crozone/iMac-G3-PC-Conversion/Docs/ek-momentum-2_rog_strix_x570-i-gaming__tehnicaldrawing.png

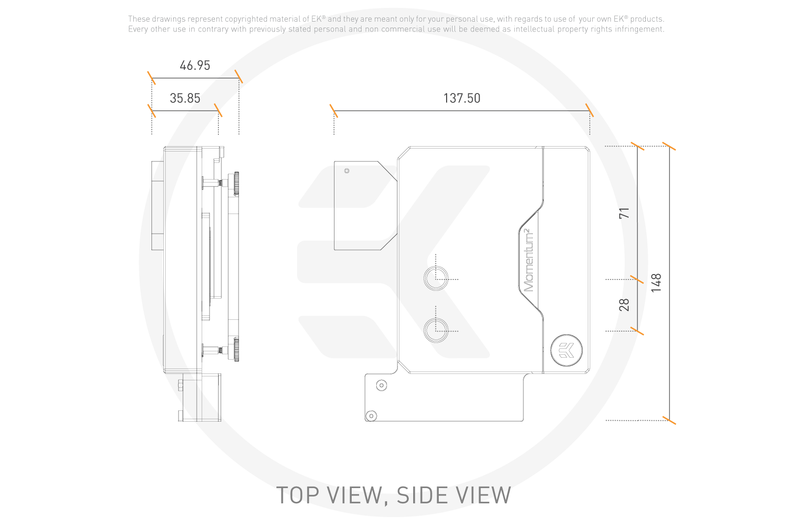
Docs/ek-momentum-2_rog_strix_x570-i-gaming__tehnicaldrawing.png
