crozone/iMac-G3-PC-Conversion/Mounting Brackets/Reservoir Mockup/Screenshots/res_0_combined.PNG

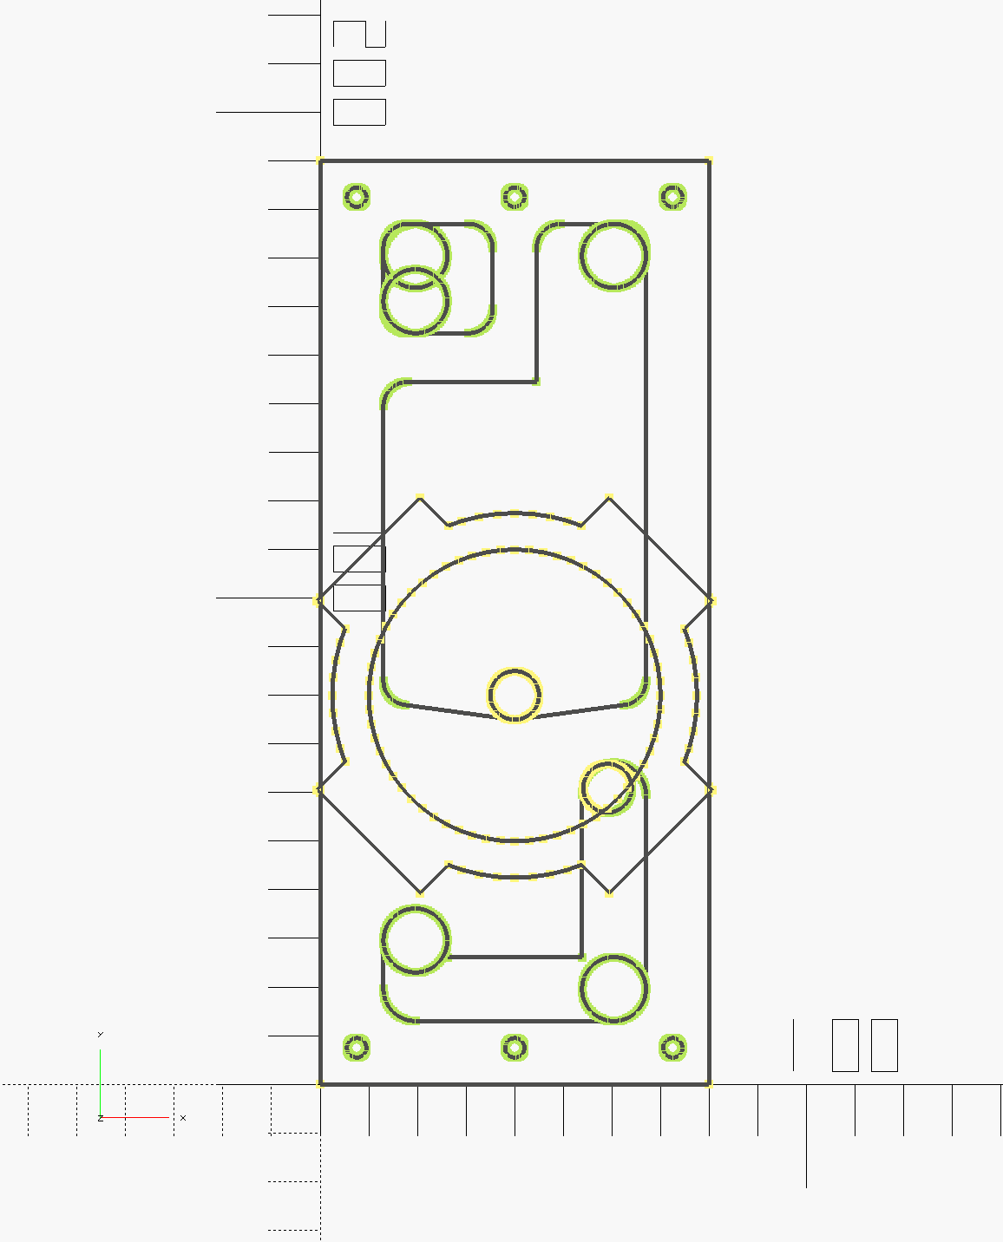
Mounting Brackets/Reservoir Mockup/Screenshots/res_0_combined.PNG
