crozone/iMac-G3-PC-Conversion/Mounting Brackets/Reservoir Mockup/Screenshots/res_2_bottom.PNG

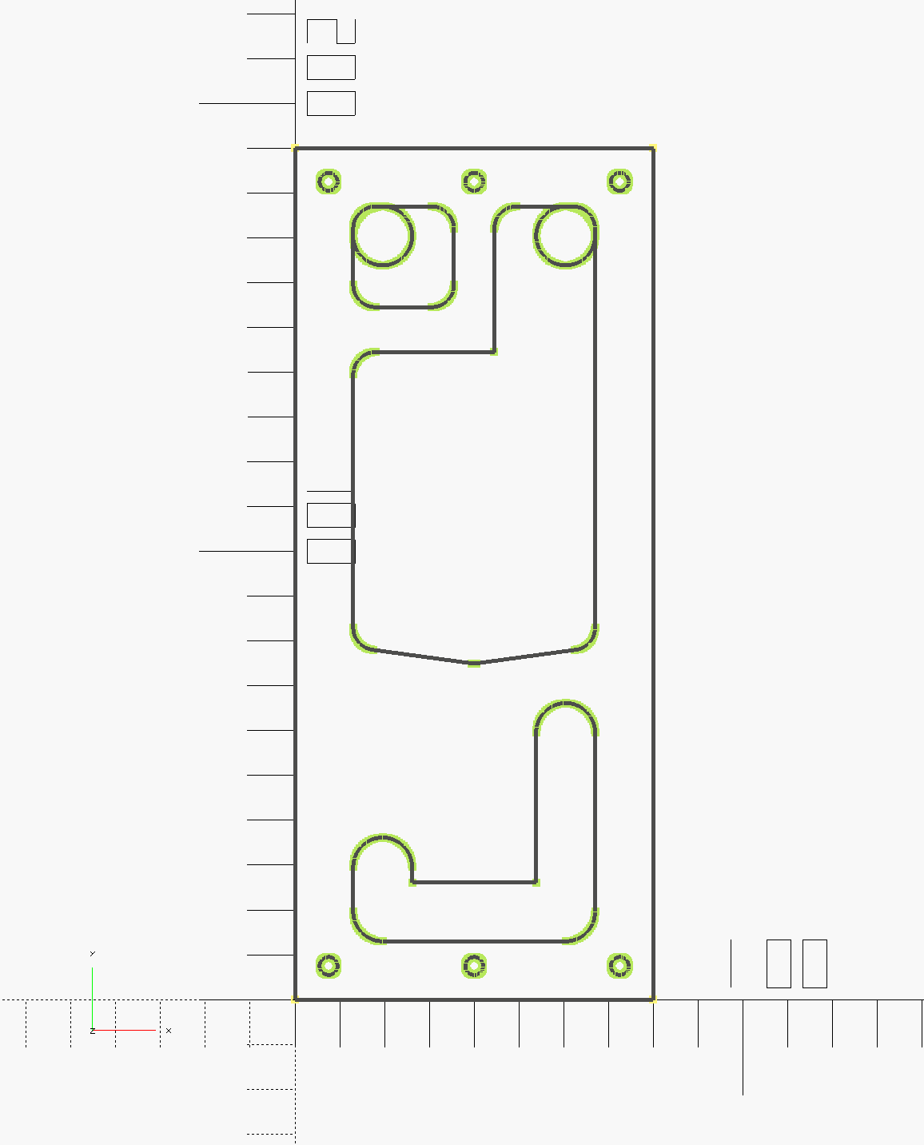
Mounting Brackets/Reservoir Mockup/Screenshots/res_2_bottom.PNG
