crozone/iMac-G3-PC-Conversion/Mounting Brackets/Reservoir Mockup/Screenshots/res_3_ortho.PNG

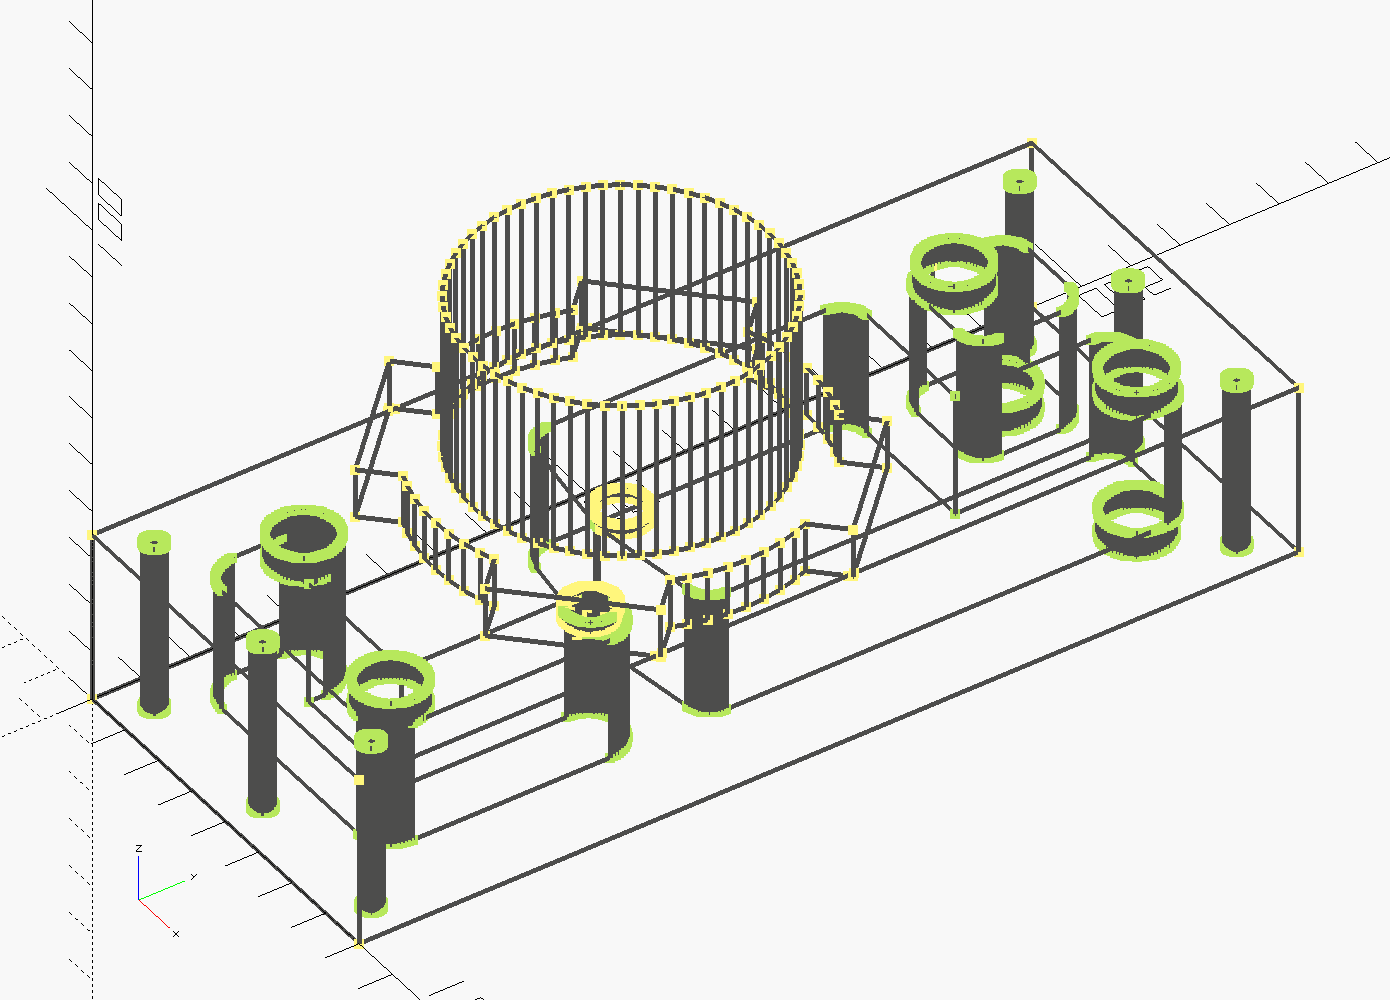
Mounting Brackets/Reservoir Mockup/Screenshots/res_3_ortho.PNG
