crozone/iMac-G3-PC-Conversion/Parts/Display Mounting/Reference Docs/LVDS Pinout.PNG

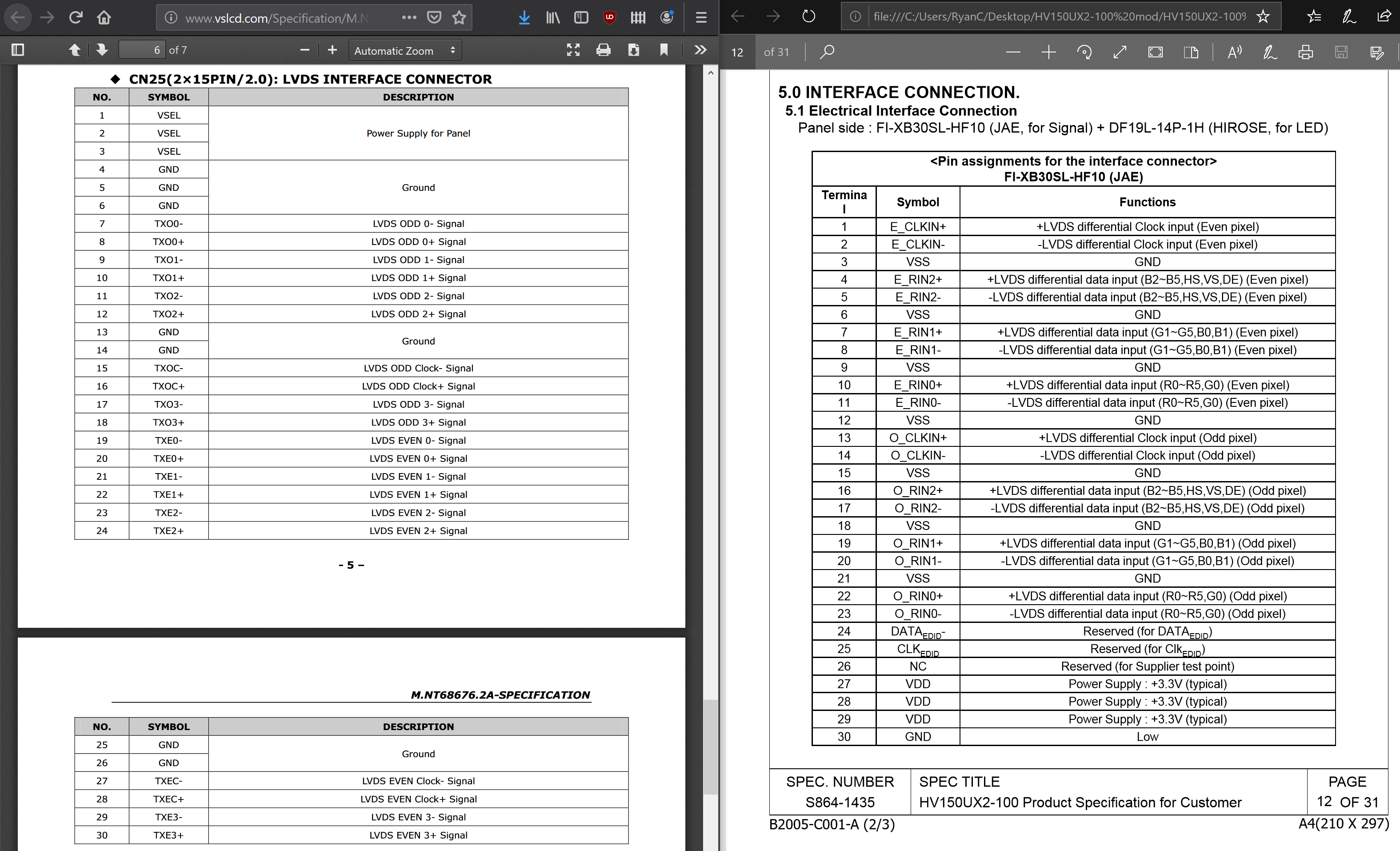
Parts/Display Mounting/Reference Docs/LVDS Pinout.PNG
