crozone/iMac-G3-PC-Conversion/Parts/Compute Sled/Docs/Bracket_drawing_1.png

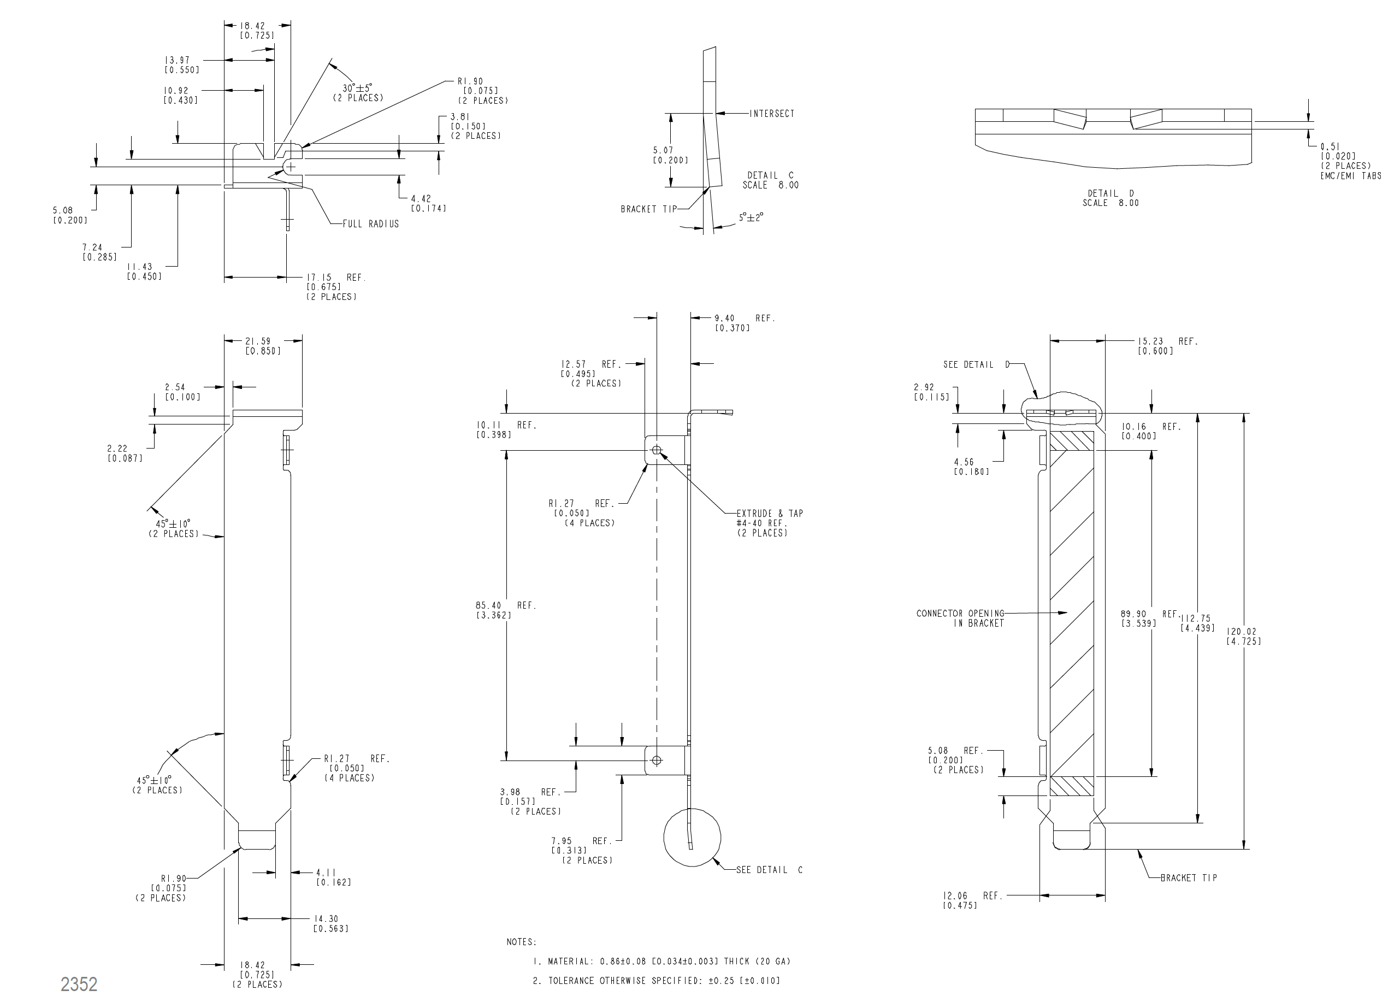
Parts/Compute Sled/Docs/Bracket_drawing_1.png
