crozone/iMac-G3-PC-Conversion/Parts/Compute Sled/Docs/Bracket_drawing_2.png

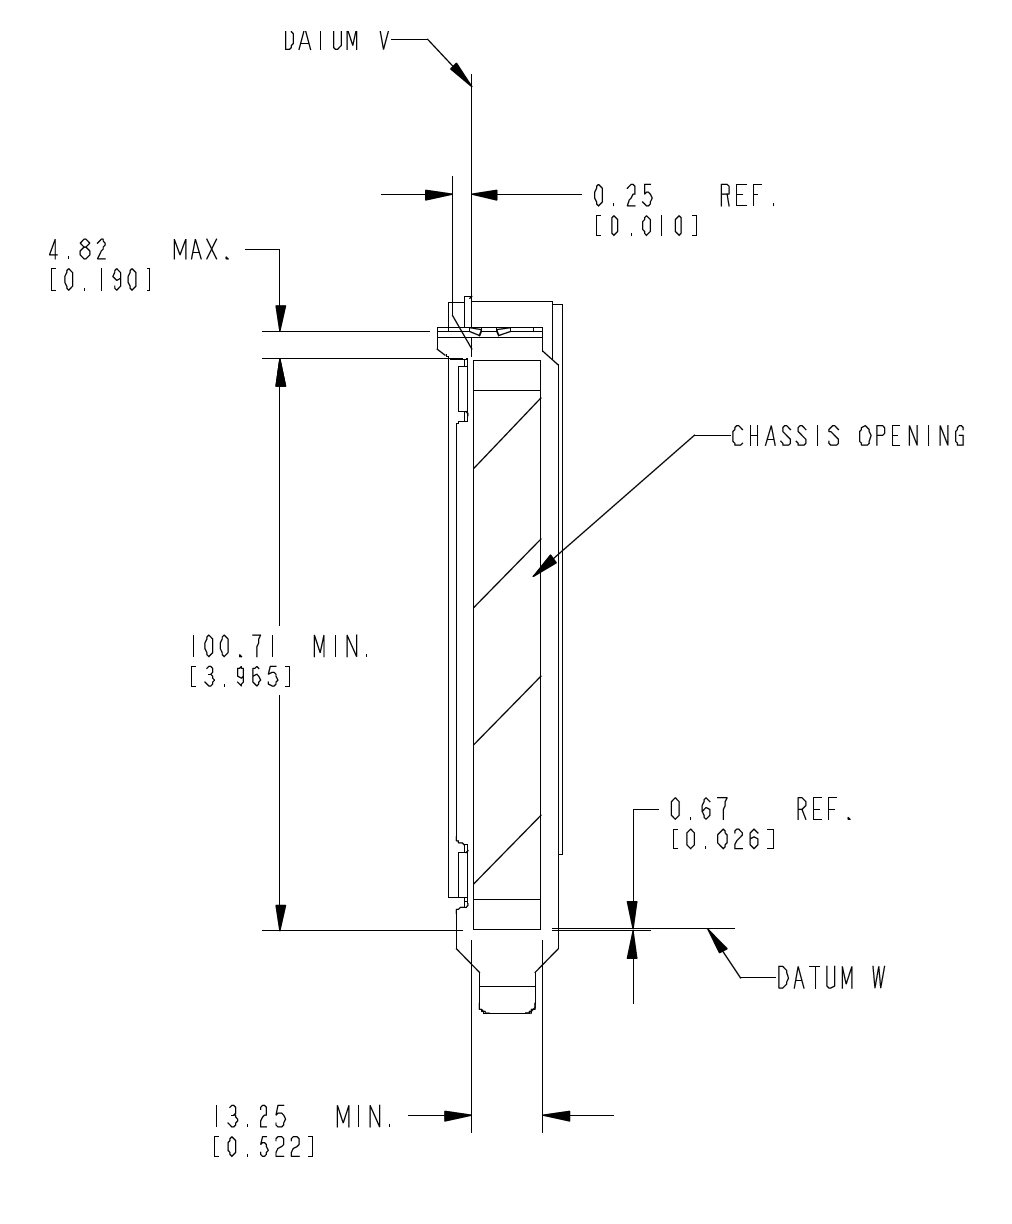
Parts/Compute Sled/Docs/Bracket_drawing_2.png
