crozone/iMac-G3-PC-Conversion/Parts/Compute Sled/Docs/hockey-stick-retention-clip.jpg

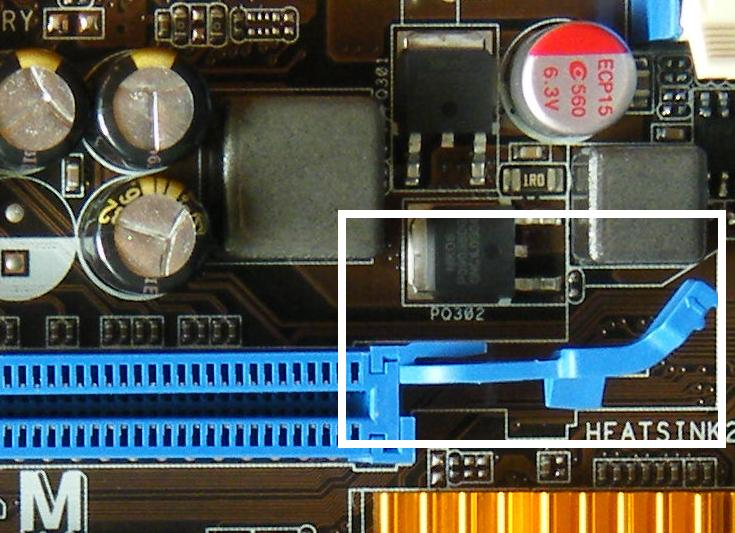
Parts/Compute Sled/Docs/hockey-stick-retention-clip.jpg
