crozone/iMac-G3-PC-Conversion/Parts/Compute Sled/Docs/mini-itx.png

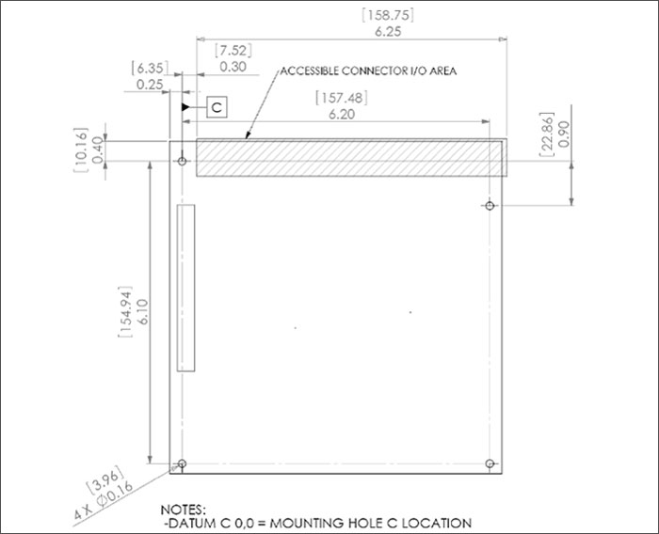
Parts/Compute Sled/Docs/mini-itx.png
