crozone/iMac-G3-PC-Conversion/Parts/Compute Sled/Docs/motherboard_drawing.png

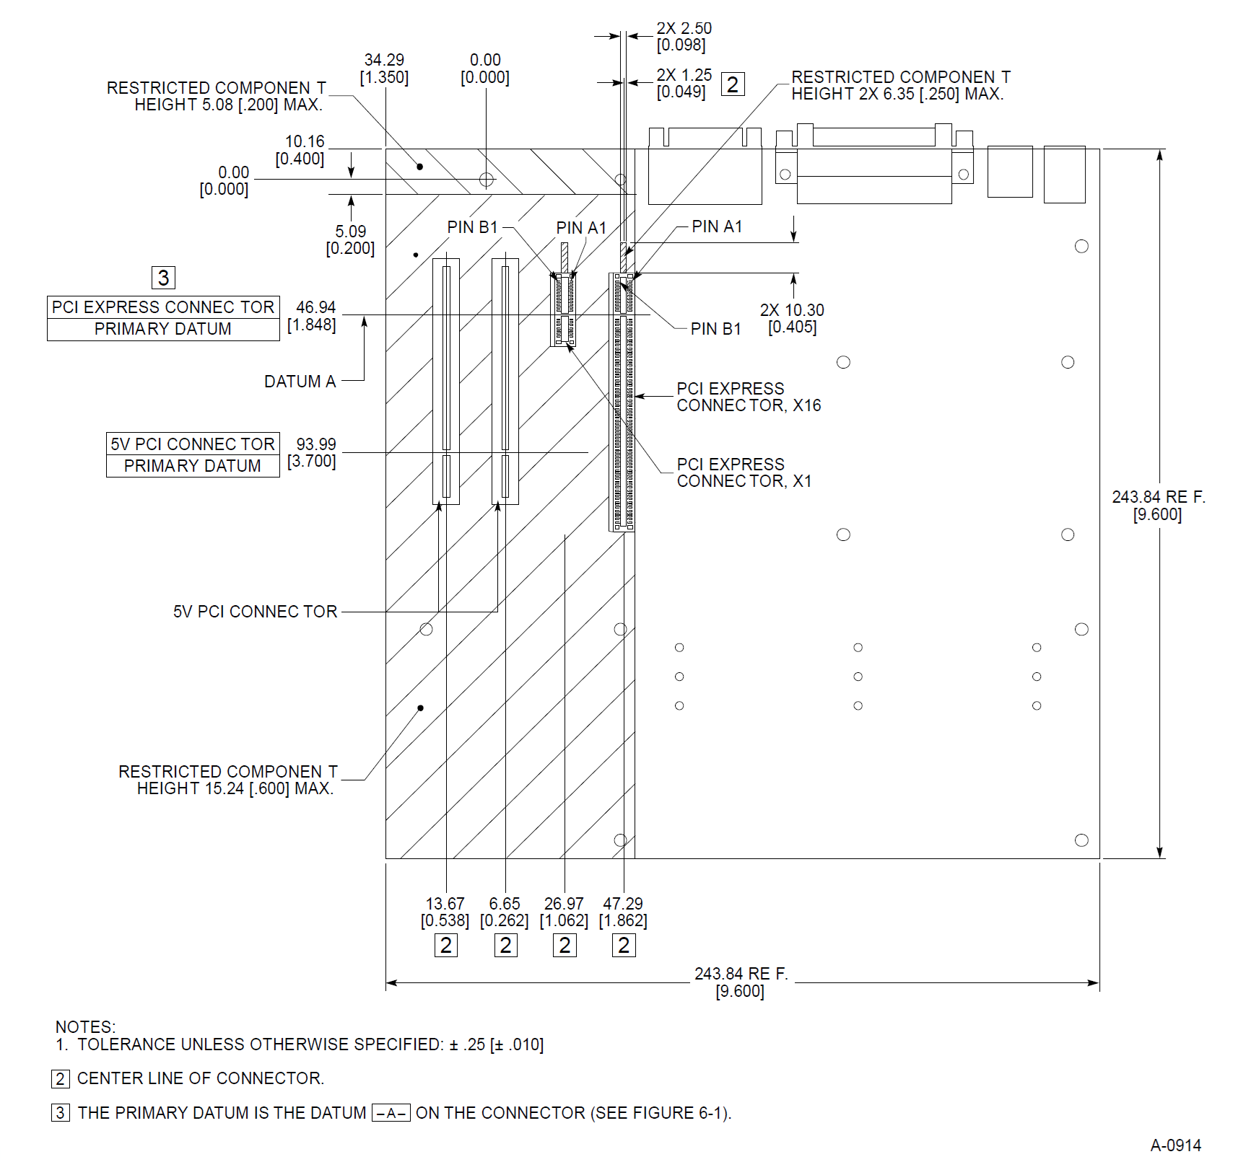
Parts/Compute Sled/Docs/motherboard_drawing.png
