crozone/iMac-G3-PC-Conversion/Parts/Compute Sled/Docs/PCIe Edge Connector Drawing.png

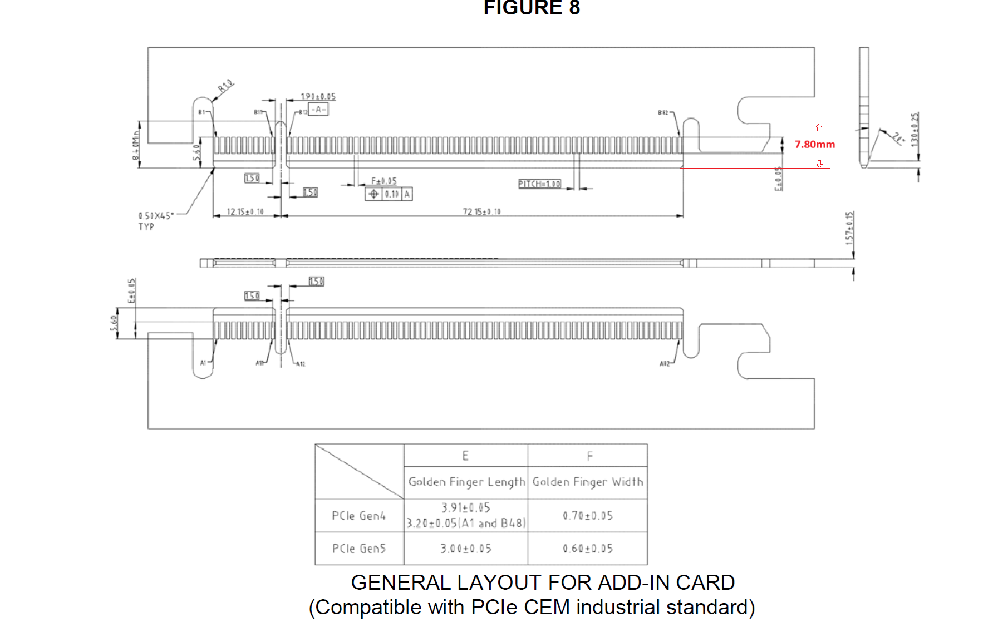
Parts/Compute Sled/Docs/PCIe Edge Connector Drawing.png
