crozone/iMac-G3-PC-Conversion/Parts/Compute Sled/Docs/PCIe_bracket_dimensions.webp

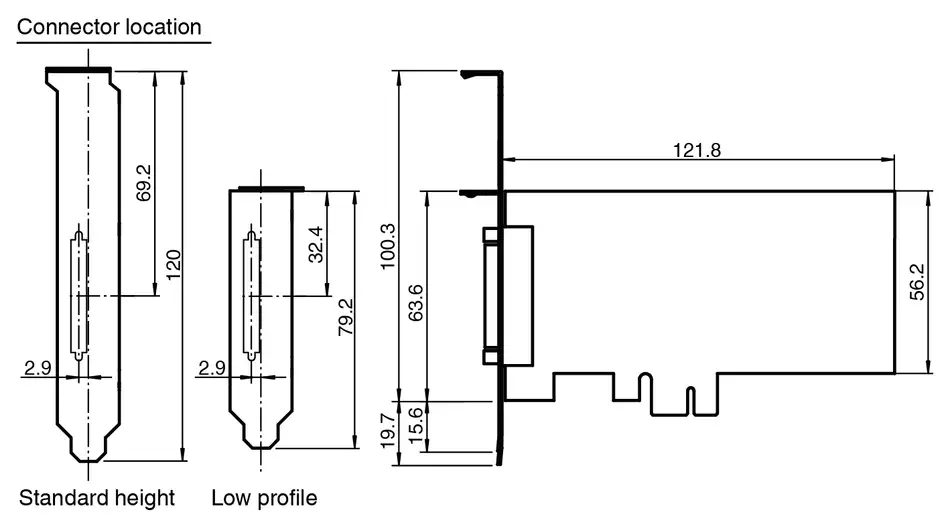
Parts/Compute Sled/Docs/PCIe_bracket_dimensions.webp
