crozone/iMac-G3-PC-Conversion/Parts/Compute Sled/Docs/PCIe_Bracket_Face_Drawing_3.jpeg

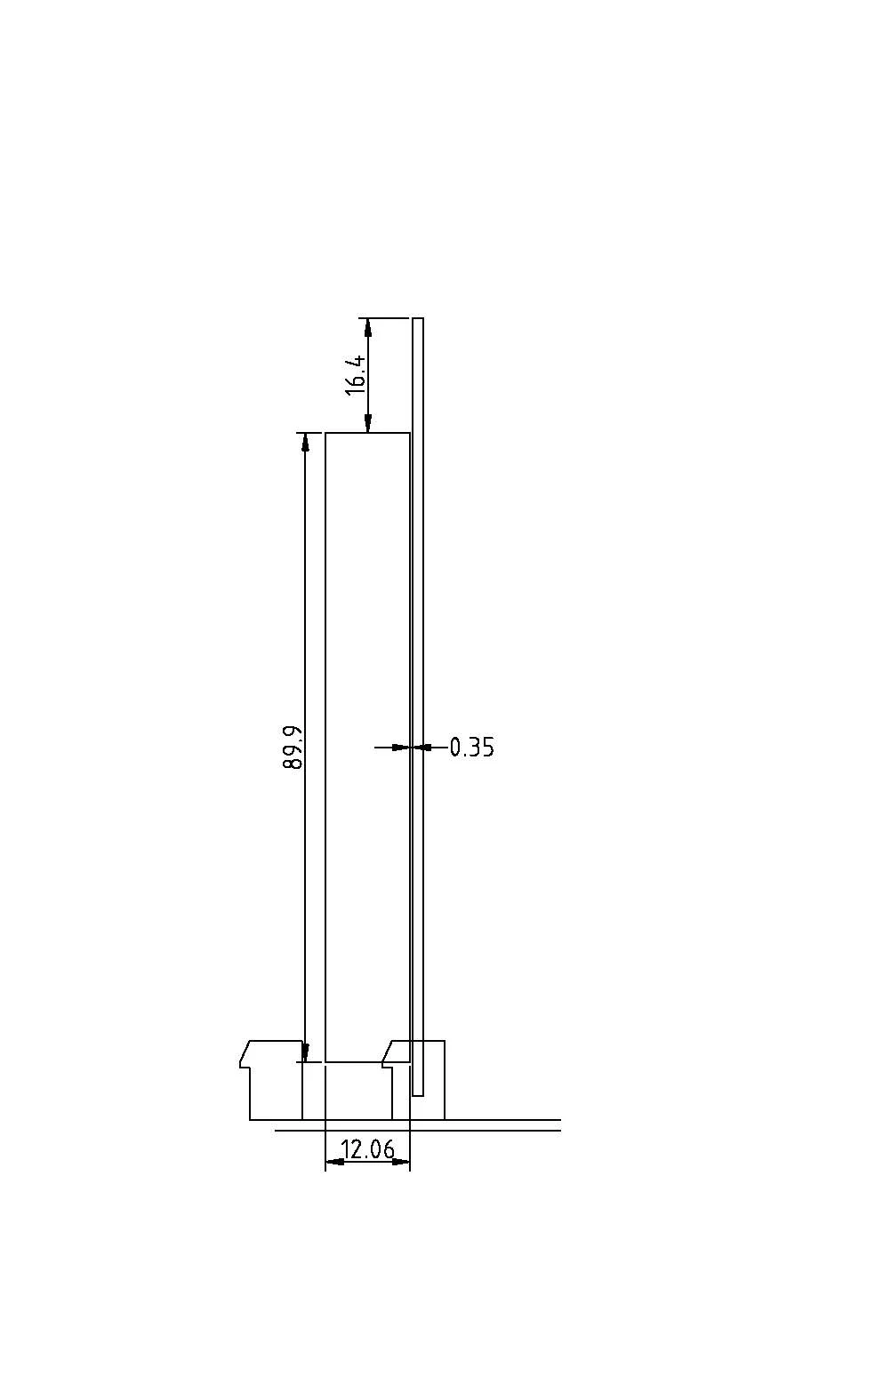
Parts/Compute Sled/Docs/PCIe_Bracket_Face_Drawing_3.jpeg
