crozone/iMac-G3-PC-Conversion/Parts/Compute Sled/Docs/PCIe_Bracket_Face_Drawing_5.jpeg

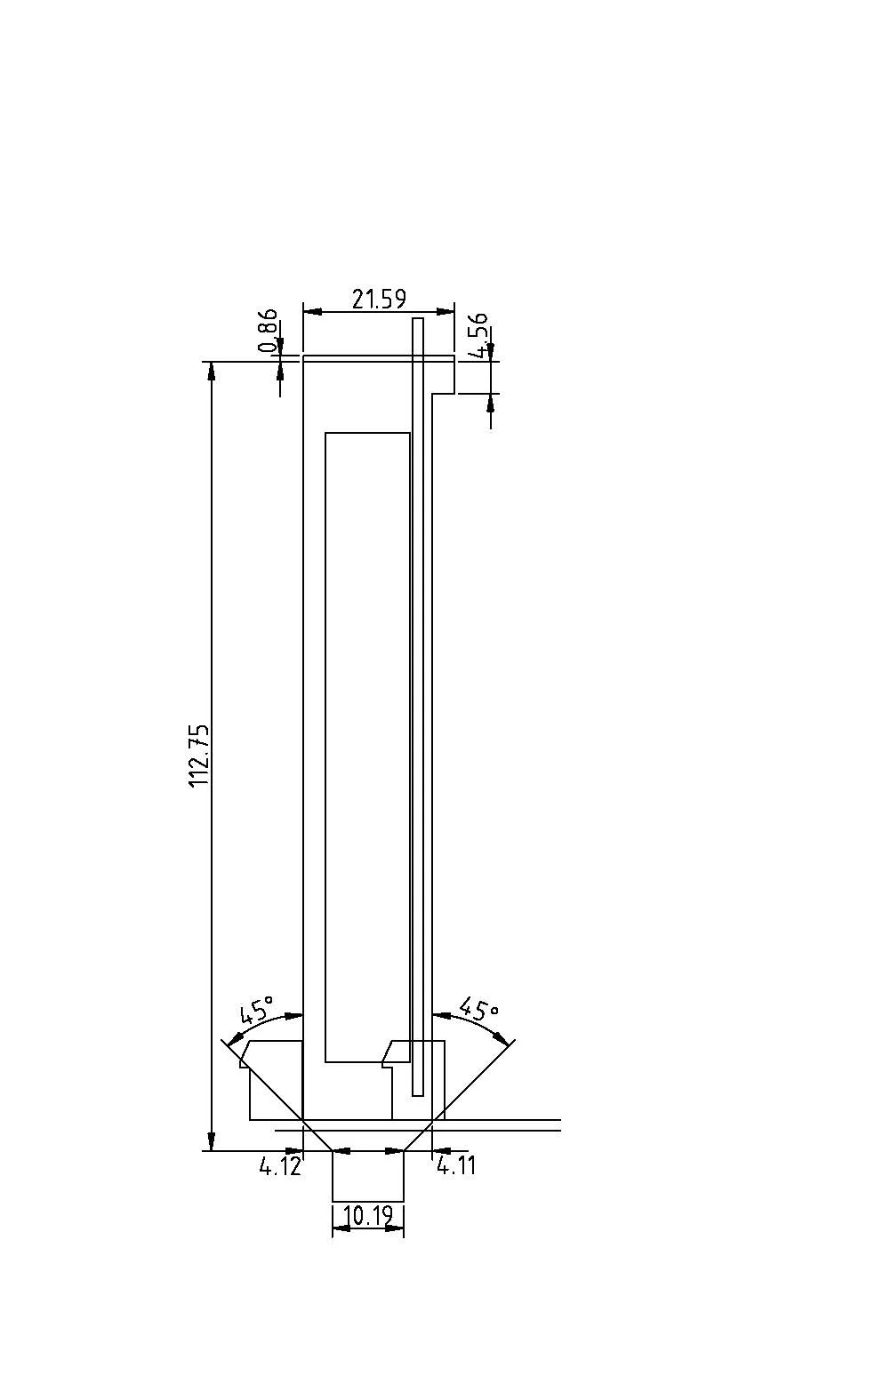
Parts/Compute Sled/Docs/PCIe_Bracket_Face_Drawing_5.jpeg
