crozone/iMac-G3-PC-Conversion/Parts/Compute Sled/Docs/PCIe_Bracket_Wing_Drawing.jpeg

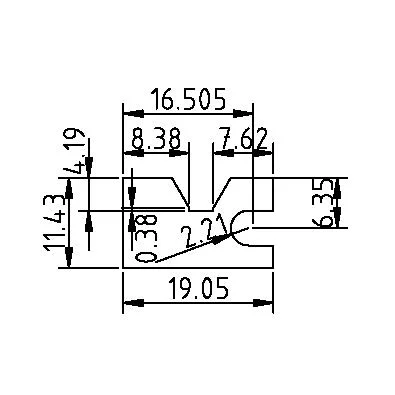
Parts/Compute Sled/Docs/PCIe_Bracket_Wing_Drawing.jpeg
