crozone/iMac-G3-PC-Conversion/Parts/Compute Sled/Docs/pcie_card_dimensions.png

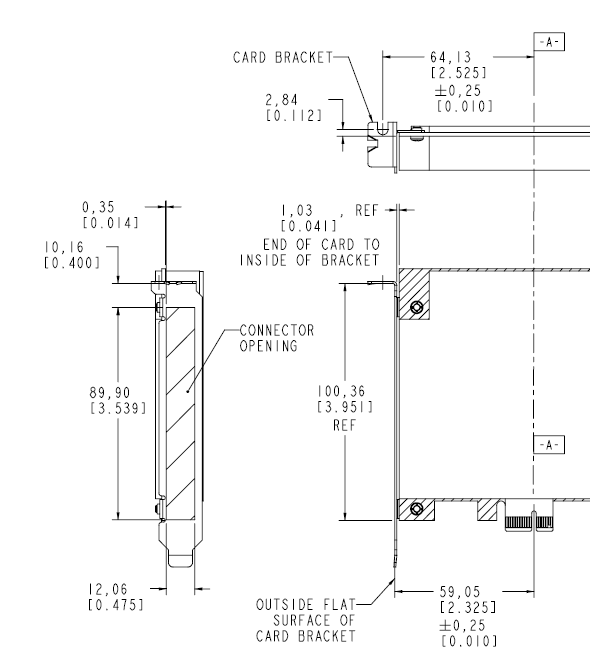
Parts/Compute Sled/Docs/pcie_card_dimensions.png
