crozone/iMac-G3-PC-Conversion/Parts/Compute Sled/Docs/PCIe_Slot_Drawing.jpeg

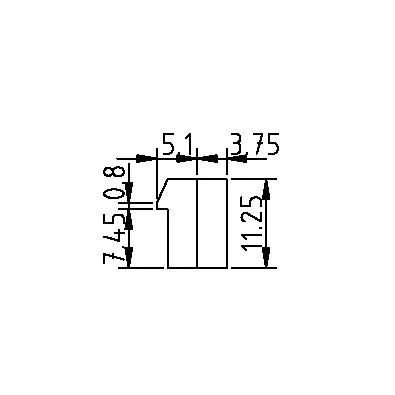
Parts/Compute Sled/Docs/PCIe_Slot_Drawing.jpeg
