crozone/iMac-G3-PC-Conversion/Parts/Compute Sled/Docs/PCIe_slot_drawing.png

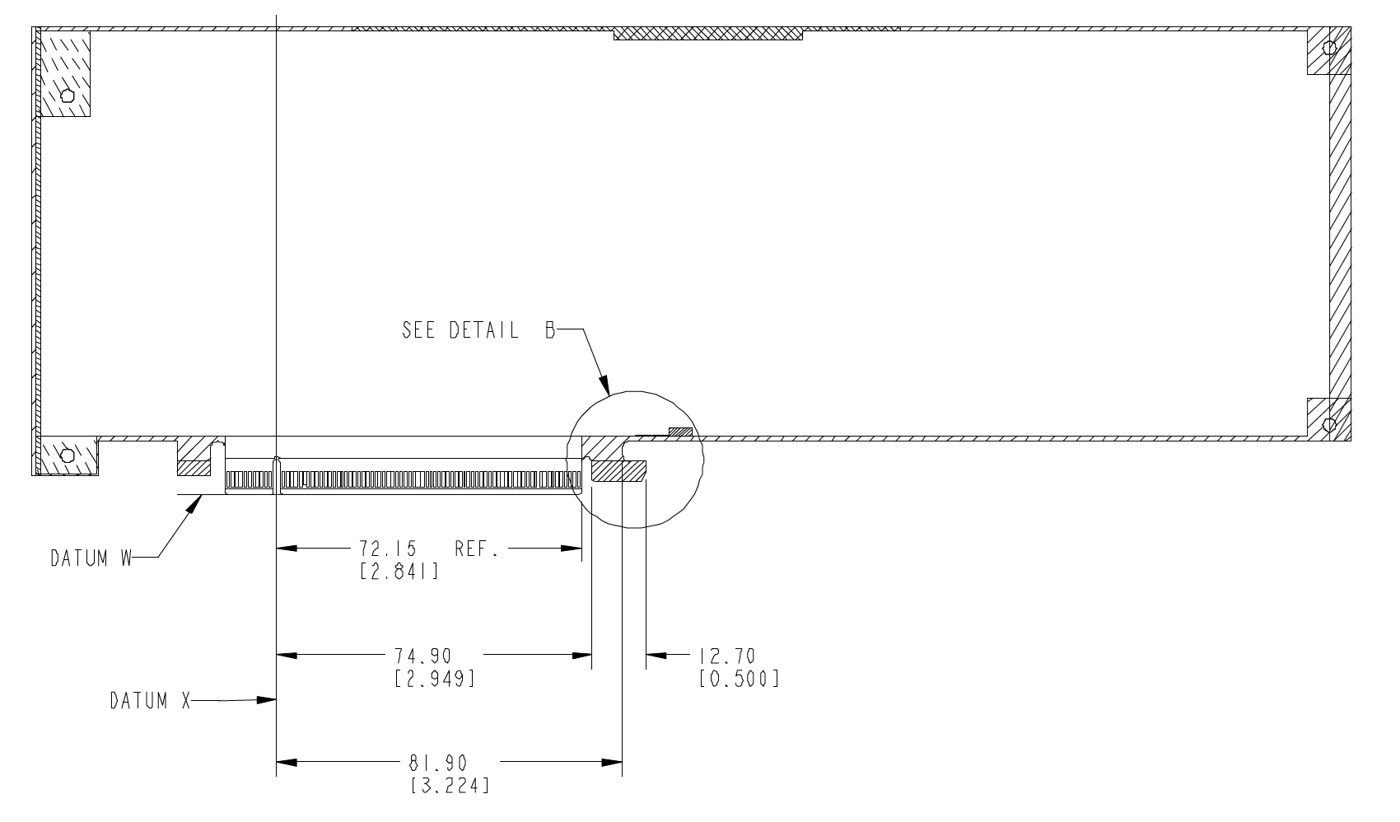
Parts/Compute Sled/Docs/PCIe_slot_drawing.png
