crozone/iMac-G3-PC-Conversion/Parts/Compute Sled/Docs/PCIe_slot_drawing_detail_B.png

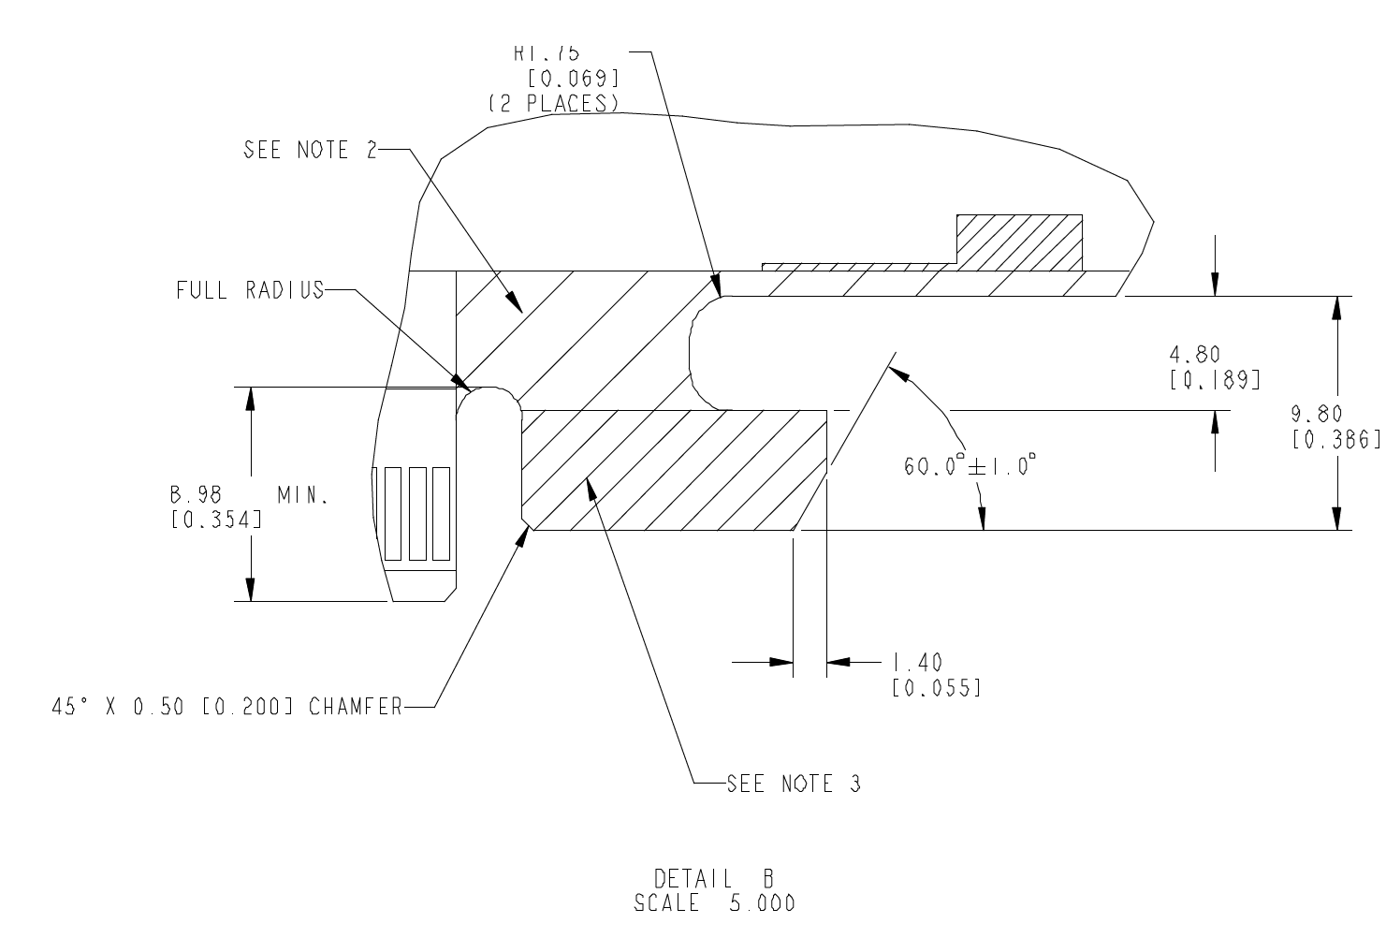
Parts/Compute Sled/Docs/PCIe_slot_drawing_detail_B.png
