crozone/iMac-G3-PC-Conversion/Parts/Display Converter Mounting/Reference Docs/40mm fan.webp

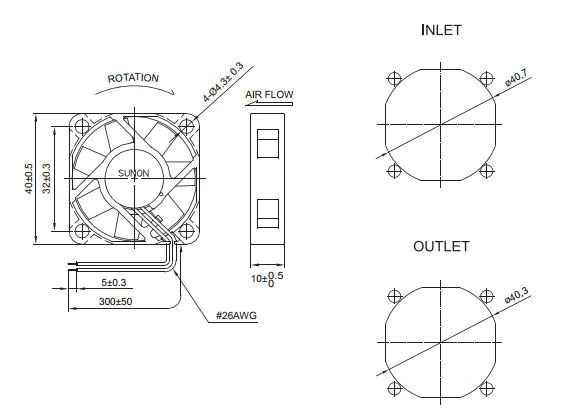
Parts/Display Converter Mounting/Reference Docs/40mm fan.webp
