crozone/iMac-G3-PC-Conversion/Parts/Display Converter Mounting/Reference Docs/Driver Layout Front.webp

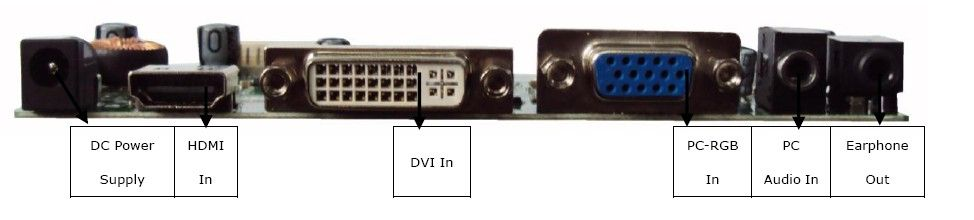
Parts/Display Converter Mounting/Reference Docs/Driver Layout Front.webp
