crozone/iMac-G3-PC-Conversion/Parts/Display Converter Mounting/Reference Docs/Driver Layout Top.webp

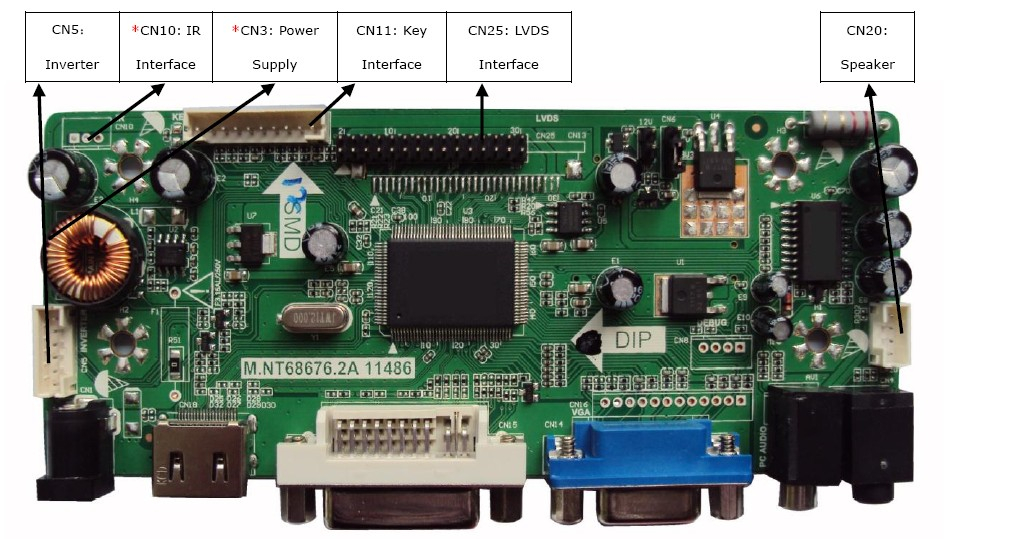
Parts/Display Converter Mounting/Reference Docs/Driver Layout Top.webp
