crozone/iMac-G3-PC-Conversion/Parts/PSU Mount/reference/SFX_diagram.JPG

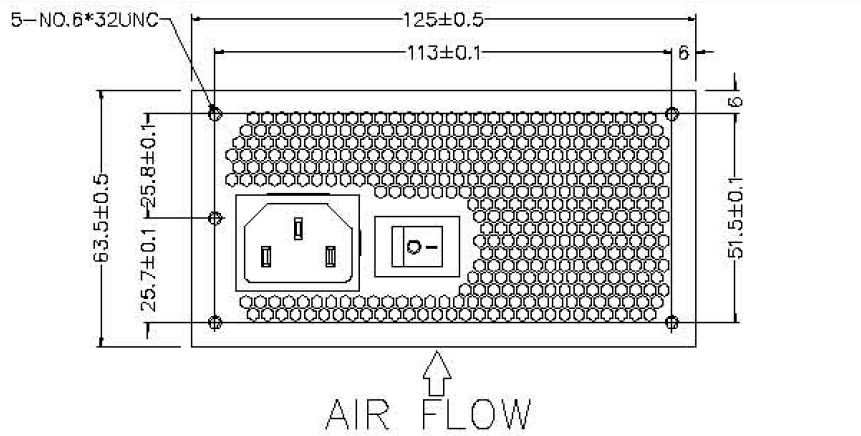
Parts/PSU Mount/reference/SFX_diagram.JPG
