crozone/iMac-G3-PC-Conversion/Parts/Display Mounting/STLs/Prototypes/display_mount_proto_1.stl

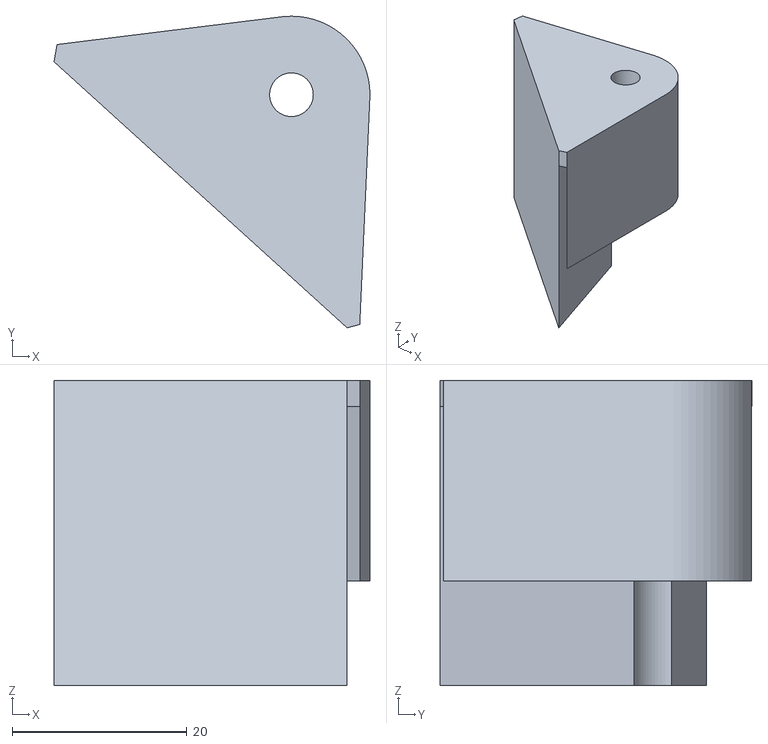
[picture p55: CAD file, 2024-05-24]
Parts/Display Mounting/STLs/Prototypes/display_mount_proto_1.stl
36.2 x 35.7 x 35.0
