crozone/iMac-G3-PC-Conversion/Parts/Display Mounting/STLs/Prototypes/mobo_bottom_left_mount_v5.stl

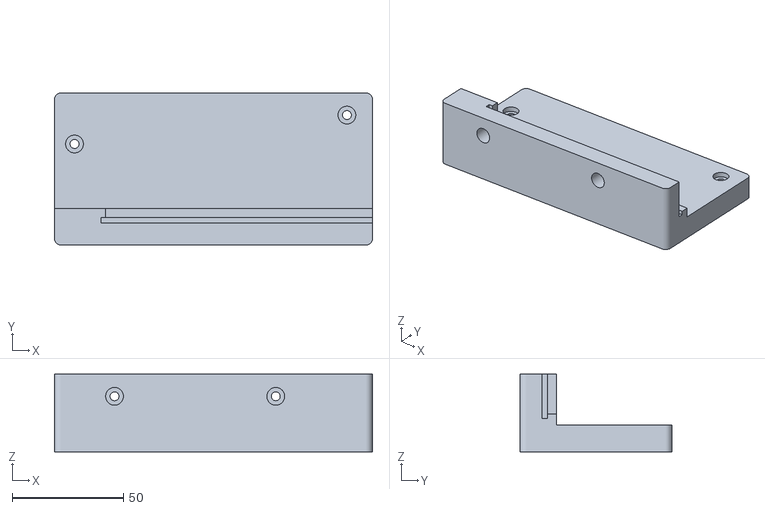
[picture p56: CAD file, 2024-05-24]
Parts/Display Mounting/STLs/Prototypes/mobo_bottom_left_mount_v5.stl
143.0 x 68.5 x 35.0
