crozone/iMac-G3-PC-Conversion/Parts/Display Mounting/STLs/Prototypes/display_mount_proto_6.stl

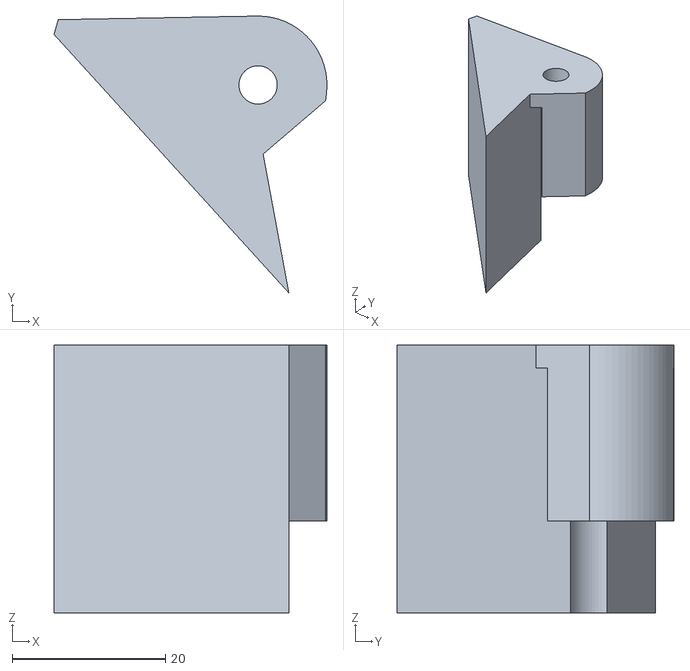
[picture p57: CAD file, 2024-05-24]
Parts/Display Mounting/STLs/Prototypes/display_mount_proto_6.stl
35.7 x 36.2 x 35.0
