crozone/iMac-G3-PC-Conversion/Parts/Display Mounting/STLs/Prototypes/display_mount_proto_5.stl

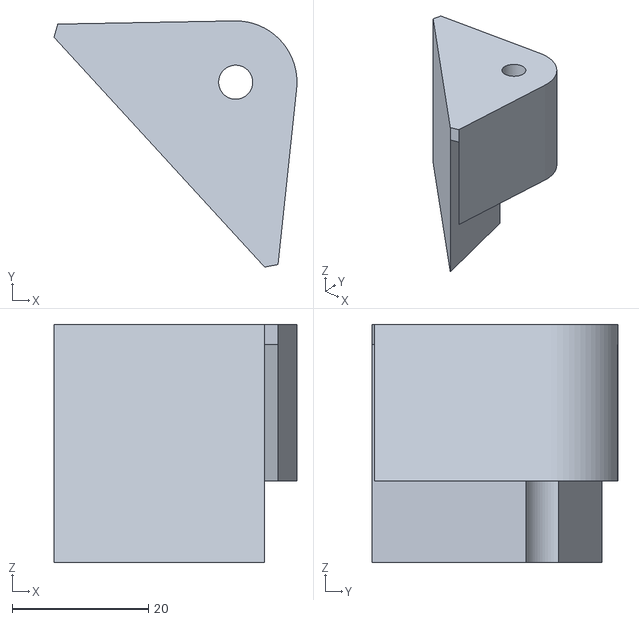
[picture p58: CAD file, 2024-05-24]
Parts/Display Mounting/STLs/Prototypes/display_mount_proto_5.stl
35.7 x 36.1 x 35.0
