crozone/iMac-G3-PC-Conversion/Parts/Display Mounting/STLs/Prototypes/upper_motherboard_plate_mount_v2.stl

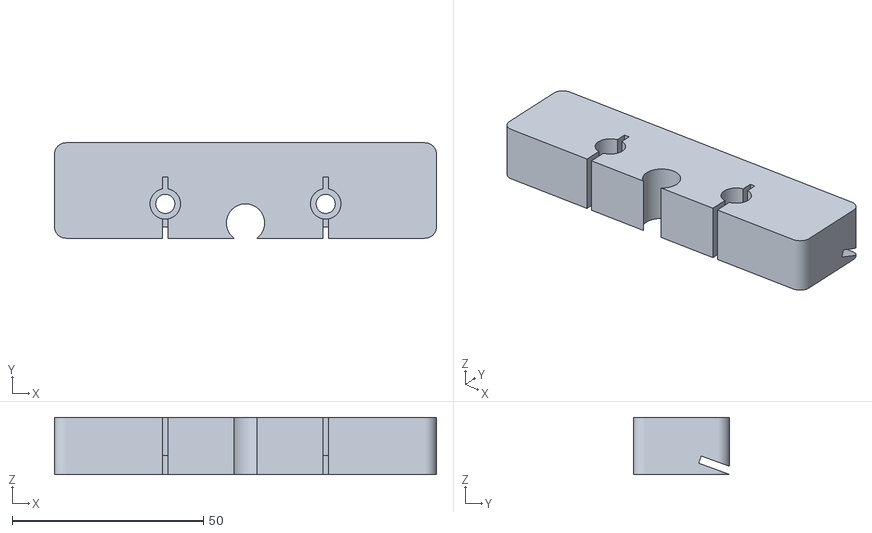
[picture p59: CAD file, 2024-05-24]
Parts/Display Mounting/STLs/Prototypes/upper_motherboard_plate_mount_v2.stl
100.0 x 25.0 x 15.0
