crozone/iMac-G3-PC-Conversion/Parts/Display Mounting/STLs/Prototypes/mobo_top_mount_2.stl

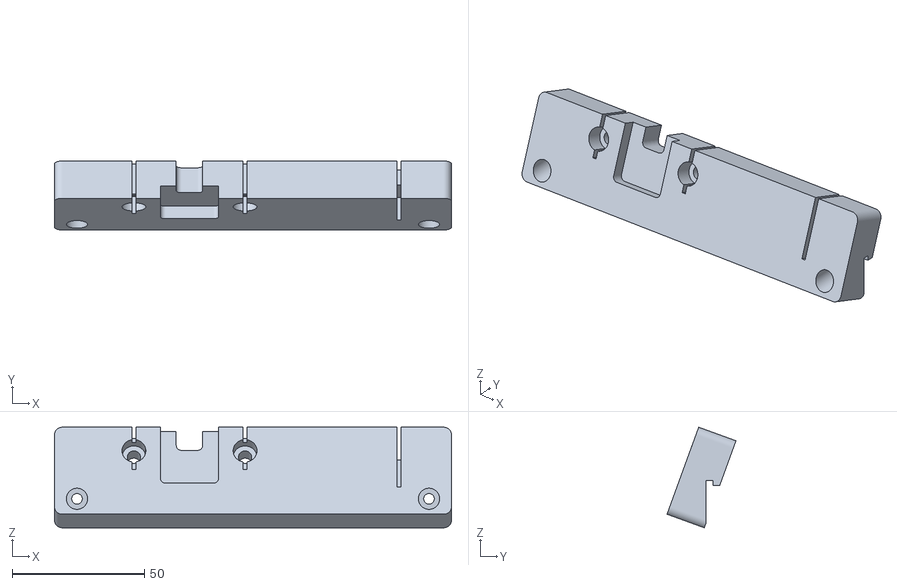
[picture p60: CAD file, 2024-05-24]
Parts/Display Mounting/STLs/Prototypes/mobo_top_mount_2.stl
150.0 x 26.1 x 38.0
