crozone/iMac-G3-PC-Conversion/Parts/Display Mounting/STLs/Prototypes/mobo_top_mount_7.stl

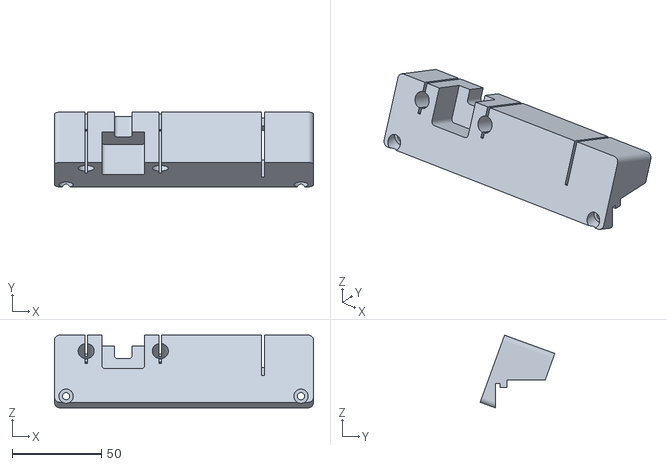
[picture p61: CAD file, 2024-05-24]
Parts/Display Mounting/STLs/Prototypes/mobo_top_mount_7.stl
145.0 x 41.9 x 40.7
