crozone/iMac-G3-PC-Conversion/Parts/Display Mounting/STLs/Prototypes/upper_motherboard_plate_mount.stl

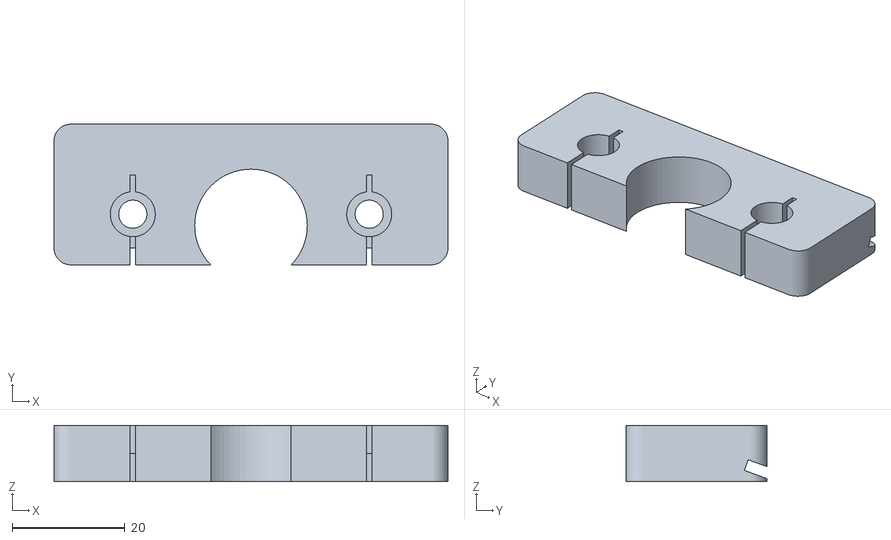
[picture p62: CAD file, 2024-05-24]
Parts/Display Mounting/STLs/Prototypes/upper_motherboard_plate_mount.stl
70.0 x 25.0 x 10.0
