crozone/iMac-G3-PC-Conversion/Parts/Display Mounting/STLs/Prototypes/mobo_top_mount_5.stl

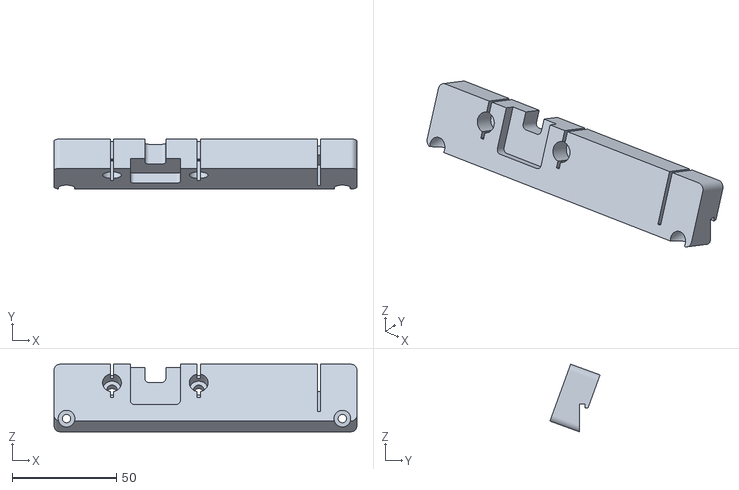
[picture p63: CAD file, 2024-05-24]
Parts/Display Mounting/STLs/Prototypes/mobo_top_mount_5.stl
145.0 x 24.0 x 32.4
