crozone/iMac-G3-PC-Conversion/Parts/Display Mounting/STLs/Prototypes/mobo_top_mount.stl

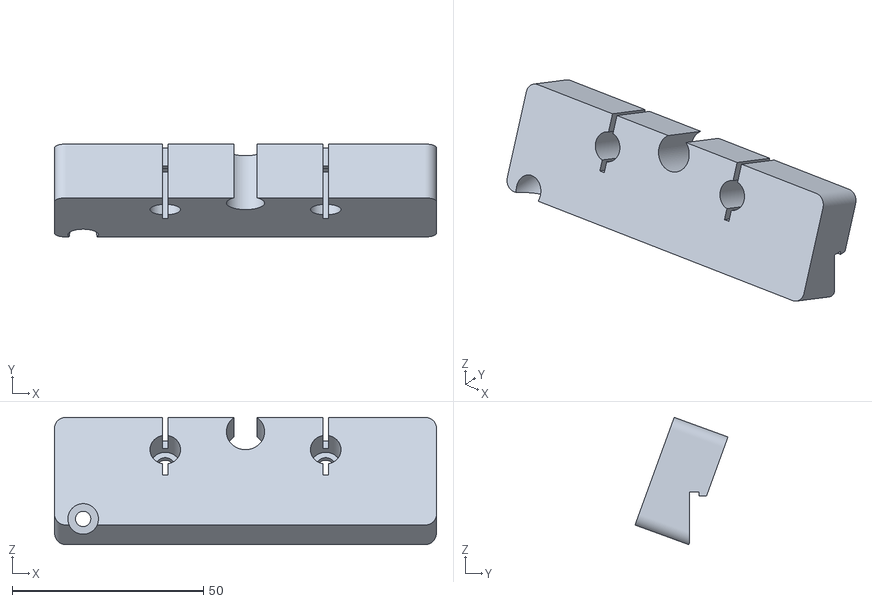
[picture p64: CAD file, 2024-05-24]
Parts/Display Mounting/STLs/Prototypes/mobo_top_mount.stl
100.0 x 24.4 x 33.3
