crozone/iMac-G3-PC-Conversion/Mounting Brackets/OpenSCAD/pci_mounting_rail.scad

// iMac G3 PCI mounting rail
// Ryan Crosby 2019
//
// All units are in mm



module pci_mounting_rail() {
    
}

pci_mounting_rail();
