crozone/iMac-G3-PC-Conversion/Parts/Pump Mount/pump_mount_2d.scad

// Pump mount.
// Ryan Crosby 2022.
//
// Vertical mouinting plate that sits to the side of the motherboard.
// Has two bulkheads for passing through liquid to the GPU

use <../Shared/2Dshapes.scad>;
use <../Shared/tab_strip.scad>;
use <../Shared/baseplate_screw_holes.scad>;
use <../Shared/rounded_corner.scad>;

include  <../Shared/shared_settings.scad>;

// Render mode:
//
// 0: 3D visual
// 1: 2D cutter layout
// 2: 2D Main Plate
// 3: 2D Bottom Plate
// 4: 2D Rear Plate
RENDER_MODE_DEFAULT = 0;

// Engrave mode:
//
// 0: Model only
// 1: Model and engrave
// 2: Engrave only

ENGRAVE_MODE_DEFAULT = 1;

// Overridden by export script
//
// 1: Cut layert
// 2: Engrave layer

EXPORT_LAYER = 0;

EXPORT_RENDER_MODE = 1;

if(EXPORT_LAYER != 0) {
    echo(str("EXPORT_LAYER enabled, set to ", EXPORT_LAYER));
}

RENDER_MODE = EXPORT_LAYER > 0 ? EXPORT_RENDER_MODE : RENDER_MODE_DEFAULT;
ENGRAVE_MODE = EXPORT_LAYER == 1 ? 0 : (EXPORT_LAYER == 2 ? 2 : ENGRAVE_MODE_DEFAULT);

echo(str("Render mode: ", RENDER_MODE));
echo(str("Engrave mode: ", ENGRAVE_MODE));

$fn = $preview ? 64 : 128;

// A very small distance to overcome rounding errors
$eps = pow(2, -15);

material_thickness = 4.5;
tab_height = material_thickness - 0.2;
top_mount_y = 203;

// How far forwards and backwards the bottom plate extends, which informs the depth of the rear bracket as well
rear_depth = 53;
front_depth = 15 + 15;

// Plate height is based directly off the top mount screw Y position.
// The top edge is always 15mm higher than the screws, less some buffer.
plate_size = [90, top_mount_y + (15 - 2)];
rear_plate_size = [rear_depth, 140];
bottom_plate_size = [plate_size[0], front_depth + rear_depth];

plate_corner_radius = [4, 4];

plate_screw_hole_diameter = 6.6;
plate_screw_hole_distance = 55;

// Bulkheads are 24mm in diameter, with 20mm thread.
bulkhead_diameter = 24;
bulkhead_hole_diameter = 20.1;
bulkhead_hole_horizontal_space = 47;
bulkhead_hole_offset = [(plate_size[0] / 2) + 2.5, 175];
bulkhead_hole_positions = [
    [bulkhead_hole_horizontal_space / 2, 0] + bulkhead_hole_offset,
    [-bulkhead_hole_horizontal_space / 2, 0] + bulkhead_hole_offset
];

// X is measured from middle of pump mount.
// Y is measured from the bottom screw of pump mount.
pump_pos = [50, 50];

rear_plate_x_offset = (plate_size[0] / 2) - (material_thickness / 2);

// Settings for placeholder GTX 295
gpu_y_start = 4;
gpu_y_length = 38;
gpu_z_start = 35;

part_name = "iMac Pump Mount";
part_version = "v1.1";

module module_label(submodule_name) {
    text_line1 = str(part_name, " // ", part_version);
    text_line2 = submodule_name;

    echo(text_line1);
    echo(text_line2);

    union() {
        text(text = text_line1, font = text_font, size = 2, halign = "center", valign = "top");

        translate([0, -4])
        text(text = text_line2, font = text_font, size = 2, halign = "center", valign = "top");
    }
}

module pump_mount_holes() {

    h_space = 54.3;
    v_space = 13.5;
    screw_hole_diameter = 3.5; // M3 screw

    hole_positions = [
        [h_space / 2, v_space],
        [-h_space / 2, v_space],
        [h_space / 2, 0],
        [-h_space / 2, 0]
    ];

    for (this_pos = hole_positions) {
        translate(this_pos)
        circle(d = screw_hole_diameter);
    }
}

module bulkhead_holes() {
    for (this_pos = bulkhead_hole_positions) {
        translate(this_pos)
        circle(d = bulkhead_hole_diameter);

        %translate(this_pos)
        circle(d = bulkhead_diameter);
    }
}

module bulkhead_labels() {
    translate([0, 12])
    translate(bulkhead_hole_offset)
    text(text = "GPU LOOP", font = text_font, size = 3, halign = "center", valign = "top");

    translate([0, bulkhead_diameter / 2 + 6]) {
        translate(bulkhead_hole_positions[0])
        text(text = "IN", font = text_font, size = 3, halign = "center", valign = "top");

        translate(bulkhead_hole_positions[1])
        text(text = "OUT", font = text_font, size = 3, halign = "center", valign = "top");
    }
}

module mount_screw_holes() {
    screw_hole_diameter = plate_screw_hole_diameter;
    vertical_tolerance = 2;

    hole_positions = [
        [-plate_screw_hole_distance / 2, 0],
        [0, 0],
        [plate_screw_hole_distance / 2, 0]];

    for (this_pos = hole_positions) {
        translate(this_pos)
        hull() {
            translate([0, -vertical_tolerance / 2])
            circle(d = screw_hole_diameter);

            translate([0, vertical_tolerance / 2])
            circle(d = screw_hole_diameter);
        }
    }
}

module cable_tie_holes() {
    h_space = 12;

    hole_positions = [
        [h_space, 0],
        [0, 0]
    ];

    for(i = [0 : 1 : 3]) {
        offset = [0, i * 40];
        for (this_pos = hole_positions) {
            translate(this_pos + offset)
            square([2, 4]);
        }
    }
}

module cables_through_hole() {
    edge_d = [3, 3];
    complexRoundSquare([20, 25], rads1=[0, 0], rads2=[0, 0], rads3=edge_d, rads4=[0, 0], center=false);

}

module pump_mount_main_2d(engrave_mode) {
    // The top plate bounds. Centered around [0,0].
    module plate() {
        // Round the top left and right corners
        // complexRoundSquare(size, top left radius, top right radius, bottom right radius, bottom left radius, center)
        union() {
            translate([0, material_thickness])
            complexRoundSquare(plate_size - [0, material_thickness], rads1=[0, 0], rads2=[0, 0], rads3=plate_corner_radius, rads4=plate_corner_radius, center=false);

            translate([plate_size[0] / 2, material_thickness - tab_height])
            tab_strip(width = plate_size[0], tab_width = 10, tab_height = tab_height + $eps, inverse = true);
        }
    }

    module rear_plate_tabs_receptacle() {
        ts_side_len = rear_plate_size[1] - material_thickness;
        translate([material_thickness, ts_side_len / 2 + material_thickness])
        rotate(90)
        tab_strip(width = ts_side_len, tab_width = 10, tab_height = tab_height + $eps, inverse = false);
    }

    module part() {
        difference() {
            plate();

            translate([plate_size[0] / 2, top_mount_y])
            mount_screw_holes();

            bulkhead_holes();

            translate(pump_pos)
            pump_mount_holes();

            translate([2, 35])
            cable_tie_holes();

            cables_through_hole();

            translate([rear_plate_x_offset, 0])
            rear_plate_tabs_receptacle();
        }
    }

    module engrave() {
        translate([68, 25])
        module_label("Front Plate");

        bulkhead_labels();
    }

    if(engrave_mode <= 1) {
        part();
    }

    if(engrave_mode >= 1) {
        #engrave();
    }
}

module pump_mount_bottom_2d(engrave_mode) {
    module plate() {
        //complexRoundSquare(bottom_plate_size, rads1=plate_corner_radius, rads2=plate_corner_radius, rads3=plate_corner_radius, rads4=plate_corner_radius, center=false);
       
        extension_width = 30;
        extension_length = 32;
        wide_length = rear_depth - extension_length;
    
        complexRoundSquare([bottom_plate_size[0], front_depth + wide_length], rads1=plate_corner_radius, rads2=[15, 15], rads3=[15, 15], rads4=plate_corner_radius, center=false);

        extension_offset = [rear_plate_x_offset - extension_width / 2 + material_thickness / 2, front_depth + wide_length - $eps];

        translate(extension_offset)
        complexRoundSquare([extension_width, extension_length + $eps], rads1=[0, 0], rads2=[0, 0], rads3=plate_corner_radius, rads4=plate_corner_radius, center=false);

        translate(extension_offset)
        {
            translate([$eps, $eps])
            translate([-10, 10])
            rotate(270)
            rounded_corner(10);

            translate([extension_width - $eps, -$eps])
            translate([10, 10])
            rotate(180)
            rounded_corner(10);
        }
    }

    module main_plate_tabs_receptacle() {
        difference() {
            translate([plate_size[0] / 2, 0])
            tab_strip(width = plate_size[0], tab_width = 10, tab_height = tab_height + $eps, inverse = true);

            translate([0, -$eps])
            square([20, tab_height + $eps * 2]);
        }
    }

    module rear_plate_tabs_receptacle() {
        ts_bot_len = rear_plate_size[0];

        translate([material_thickness, ts_bot_len / 2])
        rotate(90)
        tab_strip(width = ts_bot_len, tab_width = 10, tab_height = material_thickness, inverse = false);
    }

    module baseplate_screw_holes() {
        origin_offset = [0, 0];

        screw_positions = [
            // This 0,0 screw is supposed to be in line with the mobo mounting screws
            origin_offset + baseplate_screwhole_offset([0, 0], false),
            origin_offset + baseplate_screwhole_offset([0, 2], false),
            origin_offset + baseplate_screwhole_offset([7, 0], false),
            origin_offset + baseplate_screwhole_offset([7, 2], false),
        ];

        // Screw holes for mounting to baseplate
        for (this_pos = screw_positions) {
            translate(this_pos)
            baseplate_screw_hole();
        }
    }
    
    module part() {
        difference() {
            translate([0, -front_depth])
            plate();

            translate([0, -tab_height])
            main_plate_tabs_receptacle();

            translate([17.5 - 2, -17])
            baseplate_screw_holes();

            translate([rear_plate_x_offset, 0])
            rear_plate_tabs_receptacle();
        }
    }

    module engrave() {
        translate([plate_size[0] / 2, -15])
        module_label("Bottom Plate");
    }

    if(engrave_mode <= 1) {
        part();
    }

    if(engrave_mode >= 1) {
        #engrave();
    }
}

module pump_mount_rear_2d(engrave_mode) {
    module plate() {
        union() {
            difference() {
                translate([0, material_thickness])
                union() {
                    // Bottom
                    square([rear_plate_size[0], gpu_z_start + 10] - [0, material_thickness], center=false);

                    // First
                    complexRoundSquare([gpu_y_start, rear_plate_size[1]] - [0, material_thickness], rads1=[0,0], rads2=[0,0], rads3=plate_corner_radius, rads4=[0,0], center=false);

                    // Second
                    translate([gpu_y_start + gpu_y_length, gpu_z_start] - [0, material_thickness])
                    complexRoundSquare([rear_plate_size[0] - (gpu_y_start + gpu_y_length), 30] - [0, material_thickness], rads1=[0,0], rads2=[0,0], rads3=plate_corner_radius, rads4=plate_corner_radius, center=false);
                }

                translate([gpu_y_start, gpu_z_start])
                square([gpu_y_length, rear_plate_size[1] - gpu_z_start], center=false);
            }

            //translate([0, material_thickness])
            //complexRoundSquare(rear_plate_size - [0, material_thickness], rads1=[0,0], rads2=[0,0], rads3=plate_corner_radius, rads4=[0,0], center=false);

            ts_bot_len = rear_plate_size[0];
            translate([ts_bot_len / 2, material_thickness - tab_height])
            tab_strip(width = ts_bot_len, tab_width = 10, tab_height = tab_height + $eps, inverse = false);

            ts_side_len = rear_plate_size[1] - material_thickness;
            translate([0, ts_side_len / 2 + material_thickness])
            rotate(90)
            tab_strip(width = ts_side_len, tab_width = 10, tab_height = tab_height + $eps, inverse = false);
        }
    }
    
    module part() {
        plate();
    }

    module engrave() {
        translate([25, 15])
        module_label("Rear Plate // GPU Support");
    }

    if(engrave_mode <= 1) {
        part();
    }

    if(engrave_mode >= 1) {
        #engrave();
    }
}

module pump_mount_3d(engrave_mode) {
    color("blue")
    rotate([90, 0])
    linear_extrude(height = material_thickness) {
        pump_mount_main_2d(engrave_mode);
    }

    color("green")
    linear_extrude(height = material_thickness) {
        pump_mount_bottom_2d(engrave_mode);
    }

    color("purple")
    translate([rear_plate_x_offset, 0, 0])
    rotate([90, 00, 90])
    linear_extrude(height = material_thickness) {
        pump_mount_rear_2d(engrave_mode);
    }
}

if(RENDER_MODE == 0) {
    pump_mount_3d(ENGRAVE_MODE);
}
else if(RENDER_MODE == 1) {
    pump_mount_main_2d(ENGRAVE_MODE);

    translate([134, 153])
    rotate(270)
    pump_mount_bottom_2d(ENGRAVE_MODE);

    translate([97, 0])
    pump_mount_rear_2d(ENGRAVE_MODE);
}
else if(RENDER_MODE == 2) {
    pump_mount_main_2d(ENGRAVE_MODE);
}
else if(RENDER_MODE == 3) {
    pump_mount_bottom_2d(ENGRAVE_MODE);
}
else if(RENDER_MODE == 4) {
    pump_mount_rear_2d(ENGRAVE_MODE);
}
