crozone/iMac-G3-PC-Conversion/Parts/Shared/rounded_corner.scad

// Rounded corner module

module rounded_corner(r = 10) {
    difference() {
        square([r, r]);
        circle(r = r);
    }
}
