crozone/iMac-G3-PC-Conversion/Mounting Brackets/Reservoir Mockup/Build Pics/g3_diag_front_view.jpg

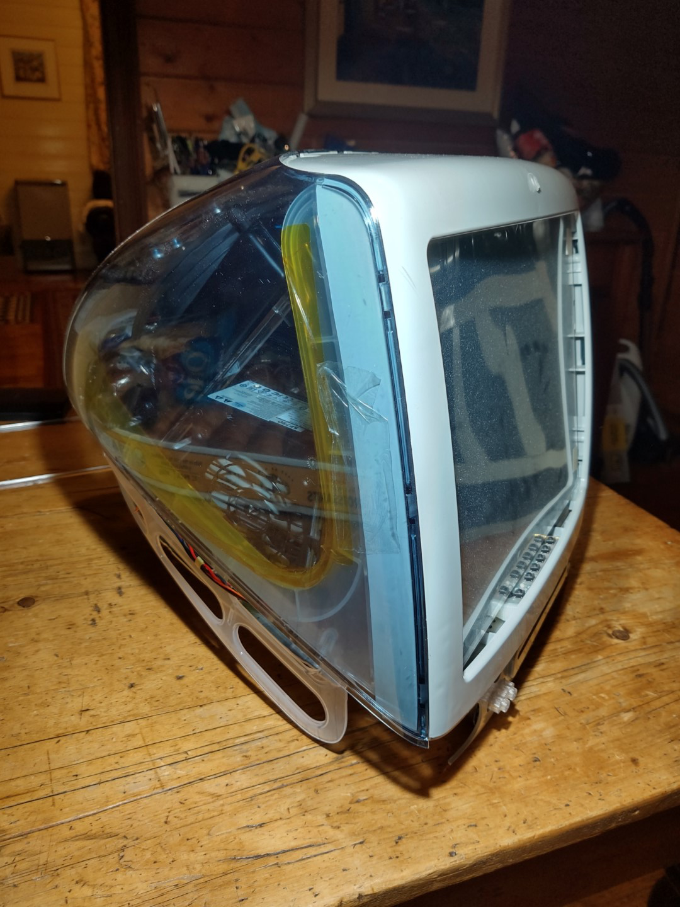
Mounting Brackets/Reservoir Mockup/Build Pics/g3_diag_front_view.jpg
