crozone/iMac-G3-PC-Conversion/Mounting Brackets/Reservoir Mockup/Build Pics/g3_reservoir_location.jpg

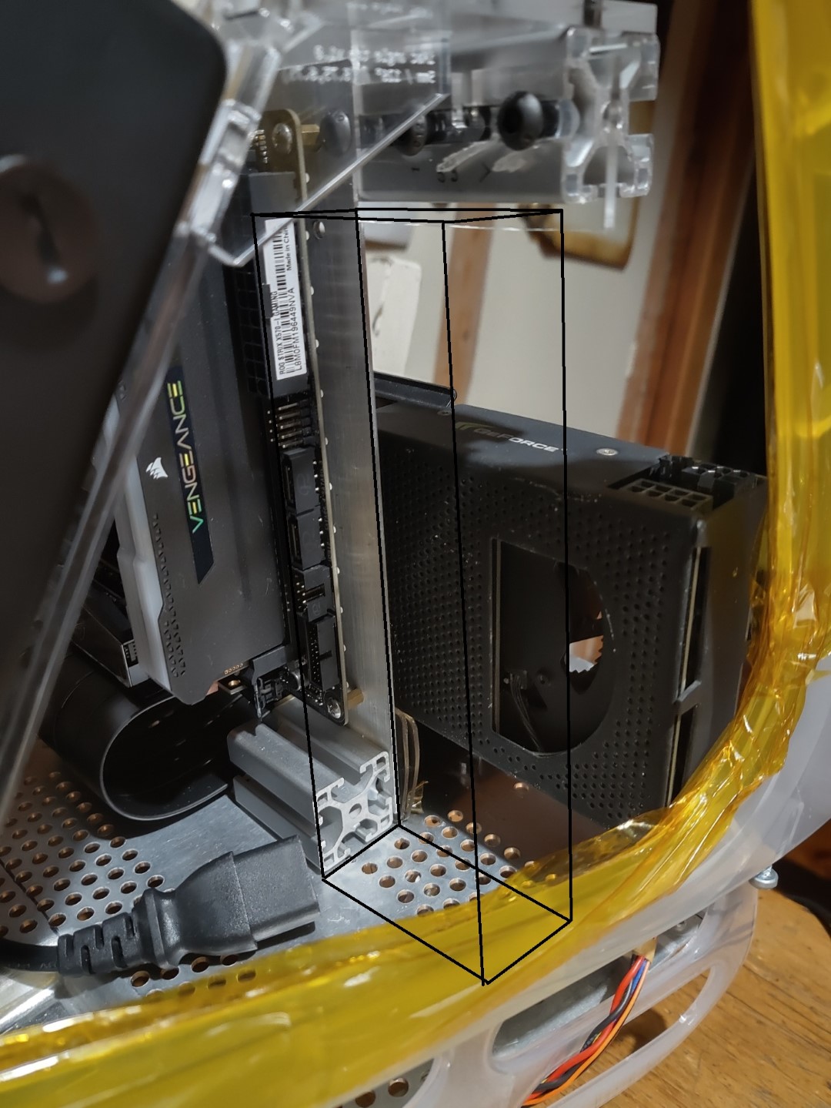
Mounting Brackets/Reservoir Mockup/Build Pics/g3_reservoir_location.jpg
