crozone/iMac-G3-PC-Conversion/Mounting Brackets/Reservoir Mockup/Build Pics/g3_side_view.jpg

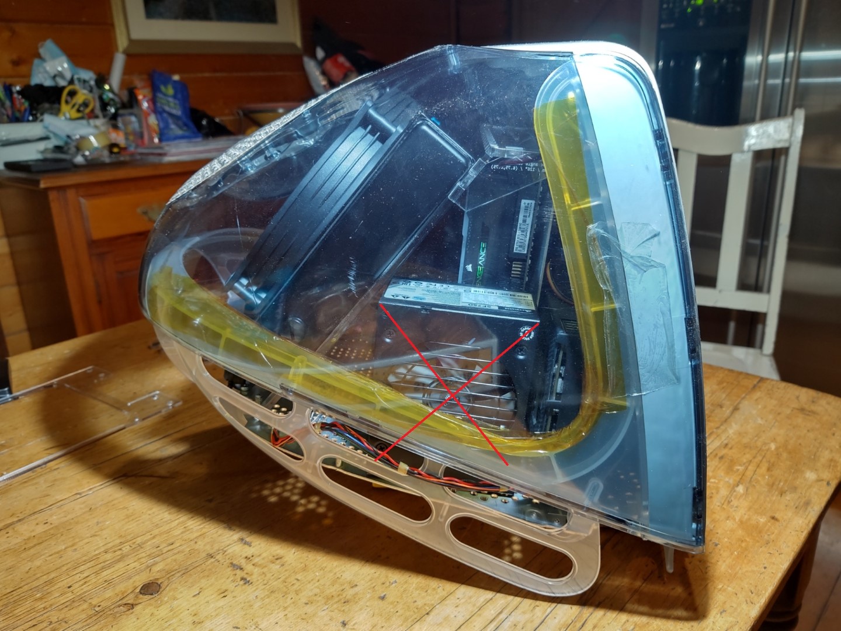
Mounting Brackets/Reservoir Mockup/Build Pics/g3_side_view.jpg
