crozone/iMac-G3-PC-Conversion/Mounting Brackets/Reservoir Mockup/Build Pics/g3_top_view_no_radiator.jpg

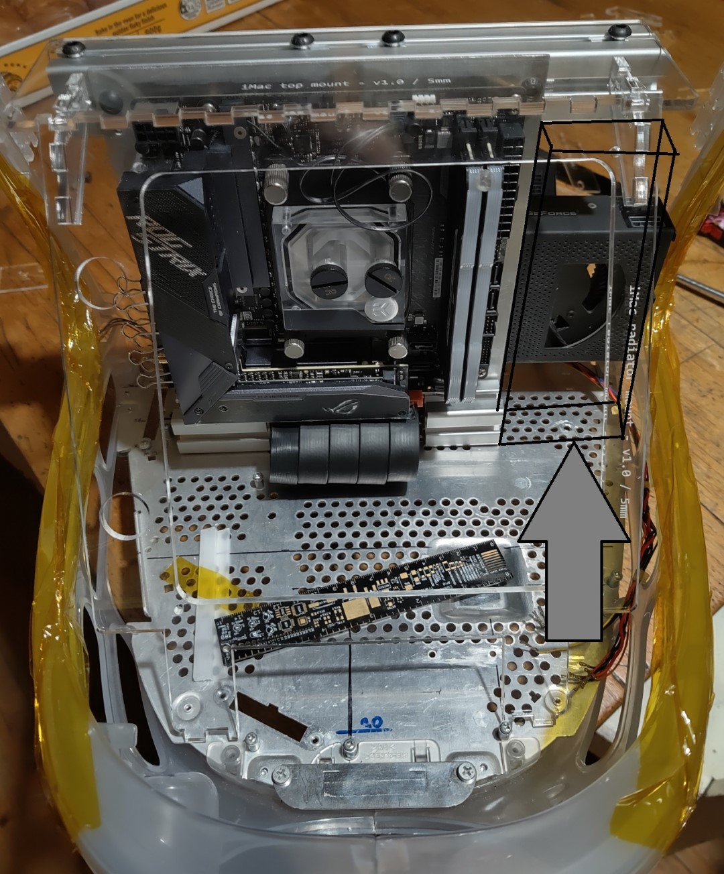
Mounting Brackets/Reservoir Mockup/Build Pics/g3_top_view_no_radiator.jpg
