crozone/iMac-G3-PC-Conversion/Parts/Display Mounting/Build Photos/Bracket br front 2.jpg

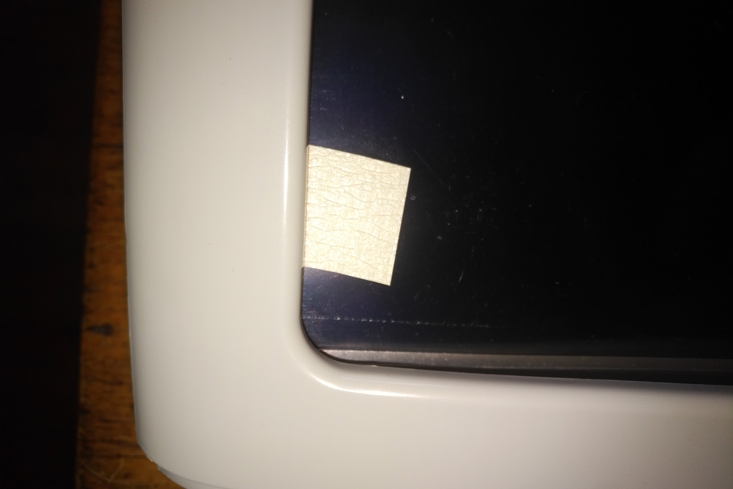
Parts/Display Mounting/Build Photos/Bracket br front 2.jpg
