crozone/iMac-G3-PC-Conversion/Parts/Display Mounting/Build Photos/Bracket br rear.jpg

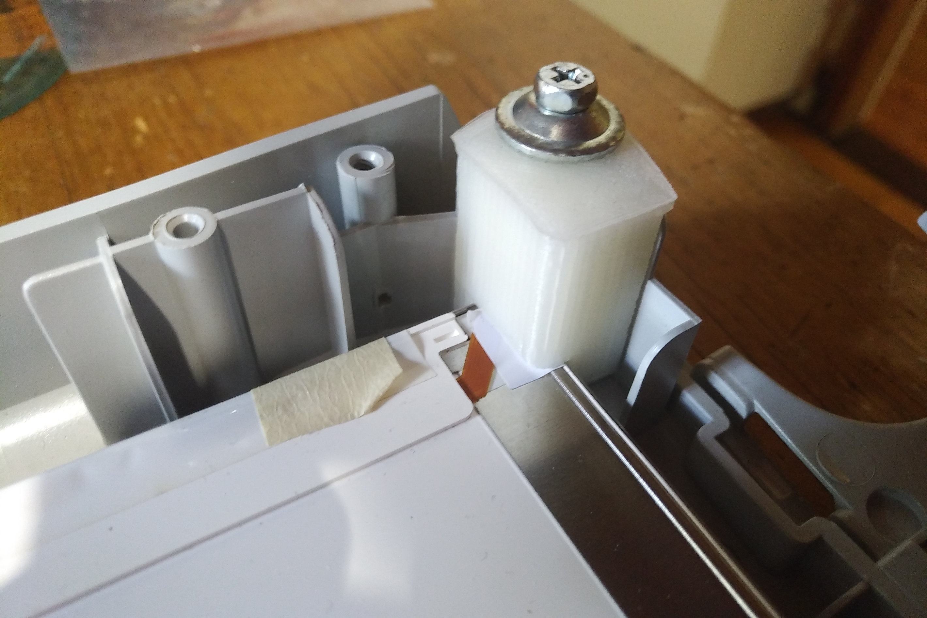
Parts/Display Mounting/Build Photos/Bracket br rear.jpg
