crozone/iMac-G3-PC-Conversion/Parts/Display Mounting/Build Photos/Brackets V3.jpg

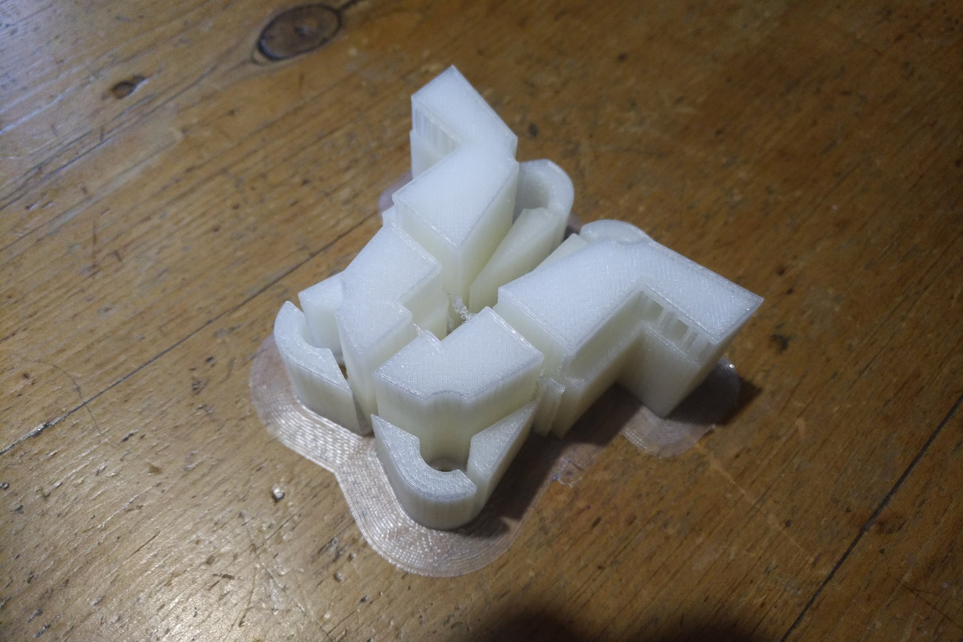
Parts/Display Mounting/Build Photos/Brackets V3.jpg
