crozone/iMac-G3-PC-Conversion/Parts/Display Mounting/Build Photos/Screen Front.jpg

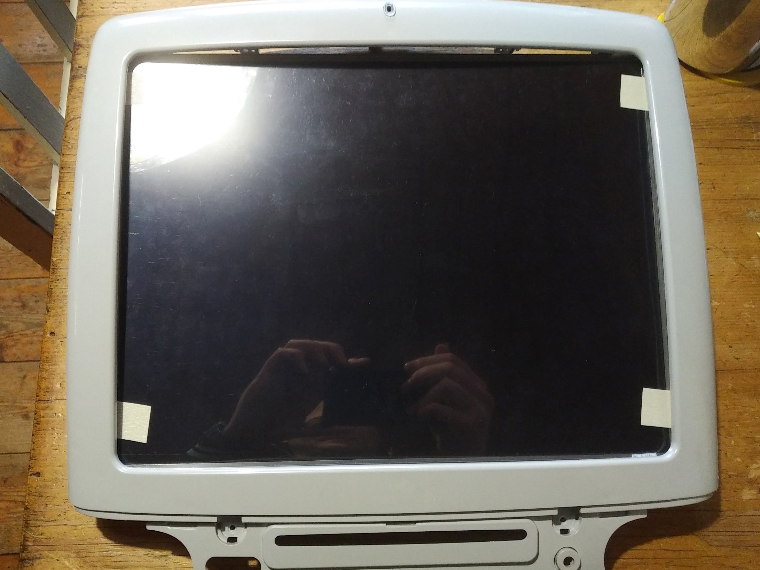
Parts/Display Mounting/Build Photos/Screen Front.jpg
